Nimfrodian/Overlord/Documentation/RelayBoard/Waveshare_Modbus_RTU_Relay_8ch_board/wiki webpage/Modbus RTU Relay - Waveshare Wiki_files/Modbus-RTU-Relay-3.png

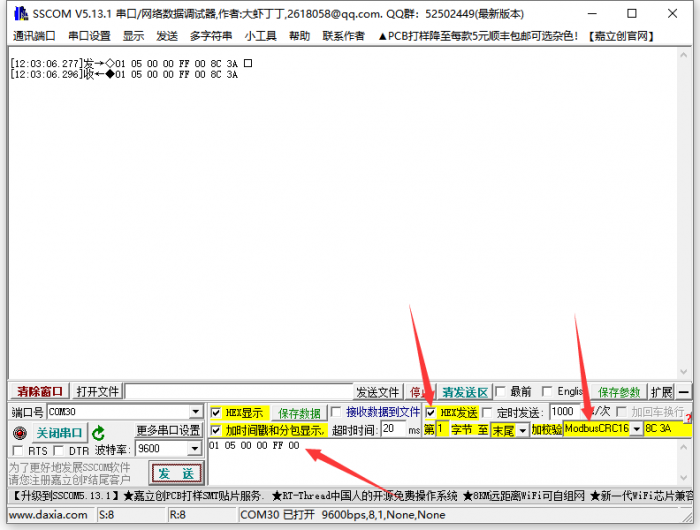
Documentation/RelayBoard/Waveshare_Modbus_RTU_Relay_8ch_board/wiki webpage/Modbus RTU Relay - Waveshare Wiki_files/Modbus-RTU-Relay-3.png
