Nimfrodian/Overlord/Documentation/RelayBoard/Waveshare_Modbus_RTU_Relay_8ch_board/wiki webpage/Modbus RTU Relay - Waveshare Wiki_files/Modbus-RTU-Relay_connet.jpg

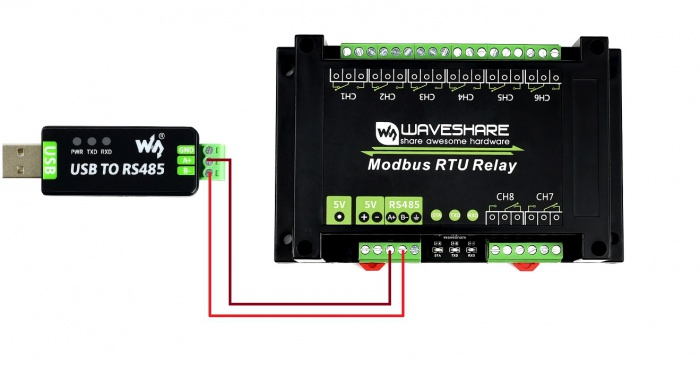
Documentation/RelayBoard/Waveshare_Modbus_RTU_Relay_8ch_board/wiki webpage/Modbus RTU Relay - Waveshare Wiki_files/Modbus-RTU-Relay_connet.jpg
