Nimfrodian/Overlord/other/tsmasterWorkspace/MiniProgram/h/TSMaster.h

#ifndef _TSMaster_MP_H
#define _TSMaster_MP_H

/*
  Note: 
  [1] Definitions of TCAN, TCANFD, TLIN, TFlexRay, TEthernetHeader can be found in this header
  [2] channel index is always starting from 0
  [3] for error codes of API, please see bottem area of this file
  [4] F3 for fast locating: TCAN TCANFD TLIN TFlexRay TEthernetHeader _TTSApp _TTSCOM _TTSTest
*/

#include <stdio.h>
#include <cstring>

#define CH1 0
#define CH2 1
#define CH3 2
#define CH4 3
#define CH5 4
#define CH6 5
#define CH7 6
#define CH8 7
#define CH9 8
#define CH10 9
#define CH11 10
#define CH12 11
#define CH13 12
#define CH14 13
#define CH15 14
#define CH16 15
#define CH17 16
#define CH18 17
#define CH19 18
#define CH20 19
#define CH21 20
#define CH22 21
#define CH23 22
#define CH24 23
#define CH25 24
#define CH26 25
#define CH27 26
#define CH28 27
#define CH29 28
#define CH30 29
#define CH31 30
#define CH32 31

#define GENERIC_STRING_MAX_LENGTH 32

typedef enum {lvlError = 1, lvlWarning = 2, lvlOK = 3, lvlHint = 4, lvlInfo = 5, lvlVerbose = 6} TLogLevel;

// basic var type definition
typedef unsigned __int8 u8;
typedef signed __int8 s8;
typedef unsigned __int16 u16;
typedef signed __int16 s16;
typedef unsigned __int32 u32;
typedef signed __int32 s32;
typedef unsigned __int64 u64;
typedef signed __int64 s64;
// pointer definition
typedef unsigned __int8* pu8;
typedef unsigned __int8** ppu8;
typedef signed __int8* ps8;
typedef unsigned __int16* pu16;
typedef signed __int16* ps16;
typedef unsigned __int32* pu32;
typedef signed __int32* ps32;
typedef signed __int32** pps32;
typedef unsigned __int64* pu64;
typedef signed __int64* ps64;
typedef float* pfloat;
typedef double* pdouble;
typedef char* pchar;
typedef char** ppchar;
typedef bool* pbool;
typedef void* pvoid;
#ifdef _WIN64
    typedef s64 native_int;
    typedef u64 ts_nfds_t;
#else
    typedef s32 native_int;
    typedef u32 ts_nfds_t;
#endif
typedef native_int* pnative_int;
typedef u32 ts_socket_t;
typedef unsigned __int32 tts_socklen_t;
typedef unsigned __int32* pts_socklen_t;
typedef u8 ts_sa_family_t;
typedef u16 ts_in_port_t;
typedef u32 ts_in_addr_t;


#define MIN(a,b) (((a)<(b))?(a):(b))
#define MAX(a,b) (((a)>(b))?(a):(b))
#define SWAP_BYTES(x) (((x) >> 8) | ((x & 0xFF) << 8))
#if defined(_MSC_VER)
    #define DLLEXPORT extern "C" __declspec(dllexport)
#else
    #define DLLEXPORT extern "C" __attribute__((visibility("default")))
#endif

#pragma pack(push)
#pragma pack(1)

// CAN definitions
#define MASK_CANProp_DIR_TX 0x01
#define MASK_CANProp_REMOTE 0x02
#define MASK_CANProp_EXTEND 0x04
#define MASK_CANProp_ERROR  0x80
#define MASK_CANProp_LOGGED 0x60

// CAN FD message properties
#define MASK_CANFDProp_IS_FD 0x01
#define MASK_CANFDProp_IS_EDL MASK_CANFDProp_IS_FD
#define MASK_CANFDProp_IS_BRS 0x02
#define MASK_CANFDProp_IS_ESI 0x04

// LIN message properties
#define MASK_LINProp_DIR_TX         0x01
#define MASK_LINProp_SEND_BREAK     0x02
#define MASK_LINProp_RECEIVED_BREAK 0x04
#define MASK_LINProp_SEND_SYNC      0x80
#define MASK_LINProp_RECEIVED_SYNC  0x10

const u8 DLC_DATA_BYTE_CNT[16] = {
    0, 1, 2, 3, 4, 5, 6, 7,
    8, 12, 16, 20, 24, 32, 48, 64
};

typedef enum _MBDDataType {
  dtInherit = 0, 
  dtDouble,
  dtSingle,
  dtHalf,
  dtInt8,
  dtUInt8,
  dtInt16,
  dtUInt16,
  dtInt32,
  dtUInt32,
  dtInt64,
  dtUInt64,
  dtBoolean,
  dtString,
} TMBDDataType, *PMBDDataType;

typedef struct _tip4_addr_t{
  u32 addr;
}tip4_addr_t, *pip4_addr_t;

typedef struct _tip6_addr_t{
  u32 addr[4];
  u32 zone;
}tip6_addr_t, *pip6_addr_t;

typedef enum {IPADDR_TYPE_V4 = 0, IPADDR_TYPE_V6 = 6, IPADDR_TYPE_ANY = 46} lwip_ip_addr_type;

typedef struct _tip_addr_t{
   tip6_addr_t ip4Or6;
   u32 FType;
   pip4_addr_t ipv4(void){
      return (pip4_addr_t)(&ip4Or6.addr[0]);
   }
   pip6_addr_t ipv6(void){
      return (pip6_addr_t)(&ip4Or6);
   }
}tip_addr_t, *pip_addr_t;

typedef struct _tts_sockaddr_private{
  u8 sa_len;
  ts_sa_family_t sa_family;
  char sa_data[14];
}tts_sockaddr_private, *pts_sockaddr;

typedef struct _ts_in_addr{
  ts_in_addr_t ts_addr;
}ts_in_addr;

#define   SIN_ZERO_LEN        (8)
typedef struct _tts_sockaddr_in_private{
  u8 sin_len;
  ts_sa_family_t sin_family;
  ts_in_port_t sin_port;
  ts_in_addr sin_addr;
  char sin_zero[SIN_ZERO_LEN];
}tts_sockaddr_in_private, pts_sockaddr_in;


typedef struct _ts_sockaddr_in_union{
  u32 FData[4];
}ts_sockaddr_in_union;

typedef struct _tts_iovec{
  void* iov_base;
  native_int iov_len;
}tts_iovec, *pts_iovec;

typedef struct _tts_timeval{
  s32 tv_sec;
  s32 tv_usec;
}tts_timeval, *pts_timeval;

#define TS_FD_SETSIZE 10
typedef struct _tts_fd_set{
  u8 fd_bits[2];
}tts_fd_set, *pts_fd_set;

typedef struct _tts_pollfd{
  s32 fd;
  s16 events; //short;
  s16 revents; //Short;
}tts_pollfd, *pts_pollfd;

typedef struct _tts_msghdr{ 
  pvoid msg_name;
  tts_socklen_t msg_namelen;
  s32 reserved0;
  pts_iovec msg_iov;
  s32 msg_iovlen;    //received package num
  s32 reserved1;
  pvoid msg_control;
  tts_socklen_t msg_controllen;
  s32 msg_flags;     //set internal
}tts_msghdr, *pts_msghdr;

typedef struct _tts_cmsghdr{
    tts_socklen_t cmsg_len;   ///* number of bytes, including header */
    s32 cmsg_level; ///* originating protocol */
    s32 cmsg_type;  ///* protocol-specific type */
}tts_cmsghdr, *pts_cmsghdr;

typedef struct _tts_in_pktinfo{
  u32 ipi_ifindex;     // Interface index
  ts_in_addr ipi_addr; // Destination (from header) address
}tts_in_pktinfo, *pts_in_pktinfo;

typedef struct _tts_addrinfo{
  s32 ai_flags;                         // Input flags
  s32 ai_family;                        // Address family of socket
  s32 ai_socktype;                      //Socket type
  s32 ai_protocol;                      // Protocol of socket
  tts_socklen_t  ai_addrlen;            // Length of socket address
  pts_sockaddr  ai_addr;                // Socket address of socket
  char*  ai_canonname;              // Canonical name of service location
  struct _tts_addrinfo*  ai_next;       // Pointer to next in list
}tts_addrinfo, *pts_addrinfo, **ppts_addrinfo;

typedef struct _tts_hostent{
  char*  h_name;          // Official name of the host
  char** h_aliases;       // A pointer to an array of pointers to alternative host names// terminated by a null pointer
  s32    h_addrtype;      // Address type
  s32    h_length;        // The length, in bytes, of the address
  char** h_addr_list;     // A pointer to an array of pointers to network addresses (in
                          // network byte order) for the host, terminated by a null pointer
}tts_hostent, *pts_hostent, **ppts_hostent;

#define LWIP_IPV6_NUM_ADDRESSES 3
//packed =  1
typedef struct _tts_net_device{
  tip4_addr_t ip_addr;
  tip4_addr_t netmask;
  tip4_addr_t gw;
  tip6_addr_t ip6_addr[LWIP_IPV6_NUM_ADDRESSES];
  u16 mtu;
  u16 mtu6;
  u16 vlan;
  u8 hwaddr[6];
  u8 flags;
  u8 index;
}tts_net_device, *pts_net_device, **ppts_net_device;

     
// CAN frame type ================================================
typedef struct _TCAN{
    u8 FIdxChn;
    u8 FProperties;
    u8 FDLC;
    u8 FReserved;
    s32 FIdentifier;
    s64 FTimeUs;
    u8  FData[8];
    // is_tx -----------------------------------------------------
    bool get_is_tx(void)
    { 
        return (FProperties & MASK_CANProp_DIR_TX) != 0;
    }
    void set_is_tx(const bool value)
    {
        if (value) {
            FProperties = FProperties | MASK_CANProp_DIR_TX;
        } else {
            FProperties = FProperties & (~MASK_CANProp_DIR_TX);
        }
    }
    __declspec(property(get = get_is_tx, put = set_is_tx)) bool is_tx;
    // is_data ----------------------------------------------------
    bool get_is_data(void)
    { 
        return (FProperties & MASK_CANProp_REMOTE) == 0;
    }
    void set_is_data(const bool value)
    {
        if (value) {
            FProperties = FProperties & (~MASK_CANProp_REMOTE);
        } else {
            FProperties = FProperties | MASK_CANProp_REMOTE;
        }
    }
    __declspec(property(get = get_is_data, put = set_is_data)) bool is_data;
    // is_std -----------------------------------------------------
    bool get_is_std(void)
    { 
        return (FProperties & MASK_CANProp_EXTEND) == 0;
    }
    void set_is_std(const bool value)
    {
        if (value) {
            FProperties = FProperties & (~MASK_CANProp_EXTEND);
        } else {
            FProperties = FProperties | MASK_CANProp_EXTEND;
        }
    }
    __declspec(property(get = get_is_std, put = set_is_std)) bool is_std;
    // is_err ----------------------------------------------------
    bool get_is_err(void)
    { 
        return (FProperties & MASK_CANProp_ERROR) != 0;
    }
    void set_is_err(const bool value)
    {
        if (value) {
            FProperties = FProperties | MASK_CANProp_ERROR;
        } else {
            FProperties = FProperties & (~MASK_CANProp_ERROR);
        }
    }
    __declspec(property(get = get_is_err, put = set_is_err)) bool is_err;
    // load data bytes -------------------------------------------
    void load_data(u8* a) {
        for (u32 i = 0; i < 8; i++) {
            FData[i] = *a++;
        }
    }
    void set_data(const u8 d0, const u8 d1, const u8 d2, const u8 d3, const u8 d4, const u8 d5, const u8 d6, const u8 d7){
        FData[0] = d0;
        FData[1] = d1;
        FData[2] = d2;
        FData[3] = d3;
        FData[4] = d4;
        FData[5] = d5;
        FData[6] = d6;
        FData[7] = d7;
    }
    // initialize with standard identifier -----------------------
    void init_w_std_id(s32 AId, s32 ADLC) {
        FIdxChn = 0;
        FIdentifier = AId;
        FDLC = ADLC;
        FReserved = 0;
        FProperties = 0;
        is_tx = false;
        is_std = true;
        is_data = true;
        *(u64*)(&FData[0]) = 0;
        FTimeUs = 0;
    }
    // initialize with extended identifier -----------------------
    void init_w_ext_id(s32 AId, s32 ADLC) {
        FIdxChn = 0;
        FIdentifier = AId;
        FDLC = ADLC;
        FReserved = 0;
        FProperties = 0;
        is_tx = false;
        is_std = false;
        is_data = true;
        *(u64*)(&FData[0]) = 0;
        FTimeUs = 0;
    }
} TCAN, *PCAN;

// CAN FD frame type =============================================
typedef struct _TCANFD{
    u8 FIdxChn;
    u8 FProperties;
    u8 FDLC;
    u8 FFDProperties;
    s32 FIdentifier;
    s64 FTimeUs;
    u8  FData[64];
    // is_tx -----------------------------------------------------
    bool get_is_tx(void)
    { 
        return (FProperties & MASK_CANProp_DIR_TX) != 0;
    }
    void set_is_tx(const bool value)
    {
        if (value) {
            FProperties = FProperties | MASK_CANProp_DIR_TX;
        } else {
            FProperties = FProperties & (~MASK_CANProp_DIR_TX);
        }
    }
    __declspec(property(get = get_is_tx, put = set_is_tx)) bool is_tx;
    // is_data ---------------------------------------------------
    bool get_is_data(void)
    { 
        return (FProperties & MASK_CANProp_REMOTE) == 0;
    }
    void set_is_data(const bool value)
    {
        if (value) {
            FProperties = FProperties & (~MASK_CANProp_REMOTE);
        } else {
            FProperties = FProperties | MASK_CANProp_REMOTE;
        }
    }
    __declspec(property(get = get_is_data, put = set_is_data)) bool is_data;
    // is_std ----------------------------------------------------
    bool get_is_std(void)
    { 
        return (FProperties & MASK_CANProp_EXTEND) == 0;
    }
    void set_is_std(const bool value)
    {
        if (value) {
            FProperties = FProperties & (~MASK_CANProp_EXTEND);
        } else {
            FProperties = FProperties | MASK_CANProp_EXTEND;
        }
    }
    __declspec(property(get = get_is_std, put = set_is_std)) bool is_std;
    // is_err ----------------------------------------------------
    bool get_is_err(void)
    { 
        return (FProperties & MASK_CANProp_ERROR) != 0;
    }
    void set_is_err(const bool value)
    {
        if (value) {
            FProperties = FProperties | MASK_CANProp_ERROR;
        } else {
            FProperties = FProperties & (~MASK_CANProp_ERROR);
        }
    }
    __declspec(property(get = get_is_err, put = set_is_err)) bool is_err;
    // is_edl ----------------------------------------------------
    bool get_is_edl(void)
    { 
        return (FFDProperties & MASK_CANFDProp_IS_FD) != 0;
    }
    void set_is_edl(const bool value)
    {
        if (value) {
            FFDProperties = FFDProperties | MASK_CANFDProp_IS_FD;
        } else {
            FFDProperties = FFDProperties & (~MASK_CANFDProp_IS_FD);
        }
    }
    __declspec(property(get = get_is_edl, put = set_is_edl)) bool is_edl;
    // is_brs ----------------------------------------------------
    bool get_is_brs(void)
    { 
        return (FFDProperties & MASK_CANFDProp_IS_BRS) != 0;
    }
    void set_is_brs(const bool value)
    {
        if (value) {
            FFDProperties = FFDProperties | MASK_CANFDProp_IS_BRS;
        } else {
            FFDProperties = FFDProperties & (~MASK_CANFDProp_IS_BRS);
        }
    }
    __declspec(property(get = get_is_brs, put = set_is_brs)) bool is_brs;
    // is_esi ----------------------------------------------------
    bool get_is_esi(void)
    { 
        return (FFDProperties & MASK_CANFDProp_IS_ESI) != 0;
    }
    void set_is_esi(const bool value)
    {
        if (value) {
            FFDProperties = FFDProperties | MASK_CANFDProp_IS_ESI;
        } else {
            FFDProperties = FFDProperties & (~MASK_CANFDProp_IS_ESI);
        }
    }
    __declspec(property(get = get_is_esi, put = set_is_esi)) bool is_esi;
    // load data bytes -------------------------------------------
    void load_data(u8* a) {
        for (u32 i = 0; i < 64; i++) {
            FData[i] = *a++;
        }
    }
    // initialize with standard identifier -----------------------
    void init_w_std_id(s32 AId, s32 ADLC) {
        s32 i;
        FIdxChn = 0;
        FIdentifier = AId;
        FDLC = ADLC;
        FProperties = 0;
        FFDProperties = MASK_CANFDProp_IS_FD;
        is_tx = false;
        is_std = true;
        is_data = true;
        for (i = 0; i < 64; i++) FData[i] = 0;
        FTimeUs = 0;
    }
    // initialize with extended identifier -----------------------
    void init_w_ext_id(s32 AId, s32 ADLC) {
        s32 i;
        FIdxChn = 0;
        FIdentifier = AId;
        FDLC = ADLC;
        FFDProperties = MASK_CANFDProp_IS_FD;
        FProperties = 0;
        is_tx = false;
        is_std = false;
        is_data = true;
        for (i = 0; i < 64; i++) FData[i] = 0;
        FTimeUs = 0;
    }
    // get fd data length ----------------------------------------
    s32 get_data_length() {
        s32 l = MIN(FDLC, 15);
        l = MAX(l, 0);
        return DLC_DATA_BYTE_CNT[l];
    }
    // to CAN struct ---------------------------------------------
    TCAN to_tcan(void){
        return *(TCAN*)(&FIdxChn);
    }
} TCANFD, *PCANFD;

// LIN frame type ================================================
typedef struct _LIN {
    u8  FIdxChn;
    u8  FErrStatus;
    u8  FProperties;
    u8  FDLC;
    u8  FIdentifier;
    u8  FChecksum;
    u8  FStatus;
    s64 FTimeUs;
    u8  FData[8];
    // is_tx -----------------------------------------------------
    bool get_is_tx(void)
    {
        return (FProperties & MASK_LINProp_DIR_TX) != 0;
    }
    void set_is_tx(const bool value)
    {
        if (value) {
            FProperties = FProperties | MASK_LINProp_DIR_TX;
        }
        else {
            FProperties = FProperties & (~MASK_LINProp_DIR_TX);
        }
    }
    __declspec(property(get = get_is_tx, put = set_is_tx)) bool is_tx;
    // load data bytes -------------------------------------------
    void load_data(u8* a) {
        for (u32 i = 0; i < 8; i++) {
            FData[i] = *a++;
        }
    }
    // initialize with identifier --------------------------------
    void init_w_id(const s32 AId, const s32 ADLC) {
        FIdxChn = 0;
        FErrStatus = 0;
        FProperties = 0;
        FDLC = ADLC;
        FIdentifier = AId;
        *(__int64*)(&FData[0]) = 0;
        FChecksum = 0;
        FStatus = 0;
        FTimeUs = 0;
    }
}TLIN, *PLIN;

// FlexRay Frame Type ============================================
typedef struct _TFlexRay {
    u8  FIdxChn;               // channel index starting from 0
    u8  FChannelMask;          // 0: reserved, 1: A, 2: B, 3: AB
    u8  FDir;                  // 0: Rx, 1: Tx, 2: Tx Request
    u8  FPayloadLength;        // payload length in bytes
    u8  FActualPayloadLength;  // actual data bytes
    u8  FCycleNumber;          // cycle number: 0~63
    u8  FCCType;               // 0 = Architecture independent, 1 = Invalid CC type, 2 = Cyclone I, 3 = BUSDOCTOR, 4 = Cyclone II, 5 = Vector VN interface, 6 = VN - Sync - Pulse(only in Status Event, for debugging purposes only)
    u8  FFrameType;            // 0 = raw flexray frame, 1 = error event, 2 = status, 3 = start cycle
    u16 FHeaderCRCA;           // header crc A
    u16 FHeaderCRCB;           // header crc B
    u16 FFrameStateInfo;       // bit 0~15, error flags
    u16 FSlotId;               // static seg: 0~1023
    u32 FFrameFlags;           // bit 0~22
                               // 0 1 = Null frame.
                               // 1 1 = Data segment contains valid data
                               // 2 1 = Sync bit
                               // 3 1 = Startup flag
                               // 4 1 = Payload preamble bit
                               // 5 1 = Reserved bit
                               // 6 1 = Error flag(error frame or invalid frame)
                               // 7 Reserved
                               // 15 1 = Async.monitoring has generated this event
                               // 16 1 = Event is a PDU
                               // 17 Valid for PDUs only.The bit is set if the PDU is valid(either if the PDU has no update bit, or the update bit for the PDU was set in the received frame).
                               // 18 Reserved
                               // 19 1 = Raw frame(only valid if PDUs are used in the configuration).A raw frame may contain PDUs in its payload
                               // 20 1 = Dynamic segment    0 = Static segment
                               // 21 This flag is only valid for frames and not for PDUs.    1 = The PDUs in the payload of this frame are logged in separate logging entries. 0 = The PDUs in the payload of this frame must be extracted out of this frame.The logging file does not contain separate  // PDU - entries.
                               // 22 Valid for PDUs only.The bit is set if the PDU has an update bit
    u32 FFrameCRC;             // frame crc
    u64 FReserved1;            // 8 reserved bytes
    u64 FReserved2;            // 8 reserved bytes
    u64 FTimeUs;               // timestamp in us
    u8  FData[254];            // 254 data bytes
    // is_tx -----------------------------------------------------
    bool get_is_tx(void){
        return FDir != 0;
    }
    void set_is_tx(const bool value){
        if (value) {
            FDir = 1;
        } else {
            FDir = 0;
        }
    }
    __declspec(property(get = get_is_tx, put = set_is_tx)) bool is_tx;
    // is_null ---------------------------------------------------
    bool get_is_null(void){
        return (FFrameFlags & ((u32)1 << 0)) != 0;
    }
    void set_is_null(const bool value){
        if (value) {
            FFrameFlags |= ((u32)1 << 0);
        } else {
            FFrameFlags &= ~((u32)1 << 0);
        }
    }
    __declspec(property(get = get_is_null, put = set_is_null)) bool is_null;
    // is_data ---------------------------------------------------
    bool get_is_data(void){
        return (FFrameFlags & ((u32)1 << 1)) != 0;
    }
    void set_is_data(const bool value){
        if (value) {
            FFrameFlags |= ((u32)1 << 1);
        } else {
            FFrameFlags &= ~((u32)1 << 1);
        }
    }
    __declspec(property(get = get_is_data, put = set_is_data)) bool is_data;
    // is_sync ---------------------------------------------------
    bool get_is_sync(void){
        return (FFrameFlags & ((u32)1 << 2)) != 0;
    }
    void set_is_sync(const bool value){
        if (value) {
            FFrameFlags |= ((u32)1 << 2);
        } else {
            FFrameFlags &= ~((u32)1 << 2);
        }
    }
    __declspec(property(get = get_is_sync, put = set_is_sync)) bool is_sync;
    // is_startup ------------------------------------------------
    bool get_is_startup(void){
        return (FFrameFlags & ((u32)1 << 3)) != 0;
    }
    void set_is_startup(const bool value){
        if (value) {
            FFrameFlags |= ((u32)1 << 3);
        } else {
            FFrameFlags &= ~((u32)1 << 3);
        }
    }
    __declspec(property(get = get_is_startup, put = set_is_startup)) bool is_startup;
    // is_pp -----------------------------------------------------
    bool get_is_pp(void){
        return (FFrameFlags & ((u32)1 << 4)) != 0;
    }
    void set_is_pp(const bool value){
        if (value) {
            FFrameFlags |= ((u32)1 << 4);
        } else {
            FFrameFlags &= ~((u32)1 << 4);
        }
    }
    __declspec(property(get = get_is_pp, put = set_is_pp)) bool is_pp;
    // is_err ----------------------------------------------------
    bool get_is_err(void){
        return (FFrameFlags & ((u32)1 << 6)) != 0;
    }
    void set_is_err(const bool value){
        if (value) {
            FFrameFlags |= ((u32)1 << 6);
        } else {
            FFrameFlags &= ~((u32)1 << 6);
        }
    }
    __declspec(property(get = get_is_err, put = set_is_err)) bool is_err;
    // is_static_segment -----------------------------------------
    bool get_is_static_segment(void){
        return (FFrameFlags & ((u32)1 << 20)) != 0;
    }
    void set_is_static_segment(const bool value){
        if (value) {
            FFrameFlags |= ((u32)1 << 20);
        } else {
            FFrameFlags &= ~((u32)1 << 20);
        }
    }
    __declspec(property(get = get_is_static_segment, put = set_is_static_segment)) bool is_static_segment;
    // initialize with slot id -----------------------------------
    void init_w_slot_id(const s32 ASlotId, const s32 ADLC) {
        FIdxChn = 0;
        FChannelMask = 1;
        FDir = 0;
        FPayloadLength = ADLC;
        FActualPayloadLength = ADLC;
        FCycleNumber = 0;
        FCCType = 5;
        FFrameType = 0;
        FHeaderCRCA = 0;
        FHeaderCRCB = 0;
        FFrameStateInfo = 0;
        FFrameFlags = 1 << 1; // data frame
        FSlotId = ASlotId;
        FFrameCRC = 0;
        FReserved1 = 0;
        FReserved2 = 0;
        FTimeUs = 0;
        for (u32 i = 0; i < 254; i++) {
            FData[i] = 0;
        }
    }
    // load data bytes -------------------------------------------
    void load_data(u8* a) {
        for (u32 i = 0; i < 254; i++) {
            FData[i] = *a++;
        }
    }
} TFlexRay, *PFlexRay;

// Ethernet Frame Type
typedef struct _TEthernetHeader{ // size = 24 B
    u8  FIdxChn;                 // Application channel index starting from 0 = Network index
    u8  FIdxSwitch;              // Network's switch index
    u8  FIdxPort;                // Network's switch's port index, 0~127: measurement port, 128~255: virtual port
    u8  FConfig;                 // 0-1: 0 = Rx, 1 = Tx, 2 = TxRq
                                 // 2: crc status, for tx, 0: crc is included in data, 1: crc is not included in data
                                 //                for rx, 0: crc is ok, 1: crc is not ok
                                 // 3: tx done type, 0: only report timestamp, 1: report full info(header+frame)
    u16 FEthernetPayloadLength;  // Length of Ethernet payload data in bytes. Max 1582 (1600 packet length - 18 header) data bytes per frame
    u16 FReserved;               // reserved for padding
    u64 FTimeUs;                 // timestamp in us
    pu8 FEthernetDataAddr;       // Ethernet data (from destination MAC to ending of payload)
#ifndef _WIN64
    u32 FPadding;                // to be compatible with x64
#endif
    u8 get_Payloads(const int index) {
        return *(ethernet_payload_addr() + index);
    }
    void set_Payloads(const int index, const u8 value) {
        *(ethernet_payload_addr() + index) = value;
    }
    __declspec(property(get = get_Payloads, put = set_Payloads)) u8 Payloads[];
    inline bool get_tx() {
        return (FConfig & 0x1) != 0;
    }
    inline void set_tx(bool a) {
        if (a) {
            FConfig |= 1;
        } else {
            FConfig &= 0xFC;
        }
    }
    void reset_data_pointer(){
        FEthernetDataAddr = actual_data_pointer();
    }
    void init(const u16 APayloadLength){
        FIdxChn = 0;
        FIdxSwitch = 0;
        FIdxPort = 0;
        FConfig = 0;
        FEthernetPayloadLength = APayloadLength;
        FReserved = 0;
        FTimeUs = 0;
        reset_data_pointer();
#ifndef _WIN64
        FPadding = 0;
#endif
        s32 i;
        pu8 p = FEthernetDataAddr;
        s32 n = MIN(1612 - 14, APayloadLength);
        n += 14;
        for (i=0; i<n; i++){
            *p++ = 0;
        }
        *(pu16)(ethernet_type_addr()) = 0x00; // IPV4 = SWAP_BYTES(0x0800)
        p = destination_mac_addr();
        for (i=0; i<6; i++){
            *p++ = 0xFF;
        }
    }
    bool is_virtual(){
        return FIdxPort >= 128;
    }
    bool is_ip_frame(){
        return ethernet_type() == 0x0800;
    }
    bool is_tcp_frame(){
        u16 o;
        has_vlans(&o);
        return (ethernet_type() == 0x0800) && (0x06 == *(FEthernetDataAddr + 0x17 + o));
    }
    bool is_udp_frame(){
        u16 o;
        has_vlans(&o);
        return (ethernet_type() == 0x0800) && (0x11 == *(FEthernetDataAddr + 0x17 + o));
    }
    pu16 first_vlan_addr(){
        return (pu16)(actual_data_pointer() + 6 + 6);
    }
    bool has_vlans(pu16 AOffsetBytes){
        *AOffsetBytes = 0;
        while (*(pu16)(actual_data_pointer() + 6 + 6 + (*AOffsetBytes)) == 0x0081){
            *AOffsetBytes = *AOffsetBytes + 4;
        }
        return *AOffsetBytes > 0;
    }
    pu8 actual_data_pointer() {
        return &FIdxChn + sizeof(_TEthernetHeader);
    }
    s32 total_ethernet_packet_length() {
        u16 o;
        has_vlans(&o);
        return sizeof(_TEthernetHeader) + 6 + 6 + 2 + o + FEthernetPayloadLength;
    }
    s32 ethernet_data_length(){
        u16 o;
        has_vlans(&o);
        return FEthernetPayloadLength + 6 + 6 + o + 2;
    }
    void set_ethernet_data_length(const u16 ALength) {
        u16 o;
        has_vlans(&o);
        o += 14;
        if (ALength > o){
            FEthernetPayloadLength = ALength - o;
        }
    }
    pu8 ethernet_payload_addr() {
        u16 o;
        has_vlans(&o);
        return FEthernetDataAddr + 6 + 6 + 2 + o;
    }
    pu8 destination_mac_addr() {
        return FEthernetDataAddr;
    }
    pu8 source_mac_addr() {
        return FEthernetDataAddr + 6;
    }
    pu8 destination_ip_addr(){
        if (!is_ip_frame()) return nullptr;
        u16 o;
        has_vlans(&o);
        return FEthernetDataAddr + 0x1E + o;
    }
    pu8 source_ip_addr(){
        if (!is_ip_frame()) return nullptr;
        u16 o;
        has_vlans(&o);
        return FEthernetDataAddr + 0x1A + o;
    }
    u16 destination_port_value(){
        if (!is_ip_frame()) return 0;
        u16 o;
        has_vlans(&o);
        o = *(u16*)(FEthernetDataAddr + 0x24 + o);
        return SWAP_BYTES(o);
    }
    u16 source_port_value(){
        if (!is_ip_frame()) return 0;
        u16 o;
        has_vlans(&o);
        o = *(u16*)(FEthernetDataAddr + 0x22 + o);
        return SWAP_BYTES(o);
    }
    pu16 ethernet_type_addr() {
        u16 o;
        has_vlans(&o);
        pu8 p = FEthernetDataAddr + 6 + 6 + o;
        return (pu16)(p);
    }
    u16 ethernet_type() {
        u16 t = *(pu16)(ethernet_type_addr());
        return SWAP_BYTES(t);
    }
    u16 get_ip_header_checksum(){
        u16 o;
        if (!is_ip_frame()) return 0;
        has_vlans(&o);
        o = *(pu16)(FEthernetDataAddr + 0x18 + o);
        return SWAP_BYTES(o);
    }
    void set_ip_header_checksum(const u16 AValue){
        u16 o;
        if (!is_ip_frame()) return;
        has_vlans(&o);
        *(pu16)(FEthernetDataAddr + 0x18 + o) = SWAP_BYTES(AValue);
    }
    void copy_payload(const pu8 ABuffer, const u16 ALength){
        u16 l = MIN(ALength, FEthernetPayloadLength);
        std::memcpy(ethernet_payload_addr(), ABuffer, l);
    }
    void set_ip_packet_payload_length(const u16 ALength){
        u16 o;
        if (!is_ip_frame()) return;
        has_vlans(&o);
        *(pu16)(FEthernetDataAddr + 16 + o) = SWAP_BYTES(ALength + 20);
    }
    u16 get_ip_packet_payload_length(){
        u16 o;
        if (!is_ip_frame()) return 0;
        has_vlans(&o);
        o = *(pu16)(FEthernetDataAddr + 16 + o);
        return SWAP_BYTES(o) - 20;
    }
    pu8 get_ip_packet_data_addr(){
        u16 o;
        if (!is_ip_frame()) return nullptr;
        has_vlans(&o);
        return FEthernetDataAddr + 0x0E + o;
    }
    pu8 get_ip_packet_payload_addr(){
        u16 o;
        if (!is_ip_frame()) return nullptr;
        has_vlans(&o);
        return FEthernetDataAddr + 0x22 + o;
    }
    void set_udp_payload_length(const u16 ALength){
        u16 o;
        if (!is_udp_frame()) return;
        has_vlans(&o);
        *(pu16)(FEthernetDataAddr + 0x26 + o) = SWAP_BYTES(ALength + 8/*header length*/);
    }
    u16 get_udp_payload_length(){
        u16 o;
        if (!is_udp_frame()) return 0;
        has_vlans(&o);
        o = *(pu16)(FEthernetDataAddr + 0x26 + o);
        return SWAP_BYTES(o) - 8/*header length*/;
    }
    pu8 get_ip_address_destination_addr(){
        u16 o;
        if (!is_ip_frame()) return 0;
        has_vlans(&o);
        return FEthernetDataAddr + 0x1E + o;
    }
    pu8 get_ip_address_source_addr(){
        u16 o;
        if (!is_ip_frame()) return 0;
        has_vlans(&o);
        return FEthernetDataAddr + 0x1A + o;
    }
    u16 get_udp_port_destination(){
        u16 o;
        if (!is_udp_frame()) return 0;
        has_vlans(&o);
        o = *(pu16)(FEthernetDataAddr + 0x24 + o);
        return SWAP_BYTES(o);
    }
    u16 get_udp_port_source(){
        u16 o;
        if (!is_udp_frame()) return 0;
        has_vlans(&o);
        o = *(pu16)(FEthernetDataAddr + 0x22 + o);
        return SWAP_BYTES(o);
    }
    void set_udp_port_destination(const u16 AValue){
        u16 o;
        if (!is_udp_frame()) return;
        has_vlans(&o);
        *(pu16)(FEthernetDataAddr + 0x24 + o) = SWAP_BYTES(AValue);
    }
    void set_udp_port_source(const u16 AValue){
        u16 o;
        if (!is_udp_frame()) return;
        has_vlans(&o);
        *(pu16)(FEthernetDataAddr + 0x22 + o) = SWAP_BYTES(AValue);
    }
    bool check_udp_fragment(pu16 AId, pu16 AOffset){
        u16 o;
        bool r;
        has_vlans(&o);
        r = (0x40 & *(FEthernetDataAddr + 0x14 + o)) == 0;
        if (r) {
            *AOffset = *(pu16)(FEthernetDataAddr + 0x14 + o);
            *AOffset = (SWAP_BYTES(*AOffset) & 0x1FFF) << 3;
            *AId = *(pu16)(FEthernetDataAddr + 0x12 + o);
            *AId = SWAP_BYTES(*AId);
        }
        return r;
    }
    pu8 get_udp_payload_addr(){
        u16 o, id, fo;
        if (!is_udp_frame()) return nullptr;        
        if (check_udp_fragment(&id, &fo)){
            if (fo > 0){
                return get_ip_packet_data_addr();
            }
        }
        has_vlans(&o);
        return FEthernetDataAddr + 0x2A + o;
    }
} TEthernetHeader, *PEthernetHeader;
typedef struct _TEthernetMAX {
    TEthernetHeader FHeader;
    u8 FBytes[1612];
    void reset_data_pointer(){
        FHeader.FEthernetDataAddr = FHeader.actual_data_pointer();
    }
} TEthernetMAX, *PEthernetMAX;

// FlexRay Cluster Parameters (size = 440)
typedef struct _TFlexRayClusterParameters {
    // general parameters
    char FShortName[GENERIC_STRING_MAX_LENGTH];
    char FLongName[GENERIC_STRING_MAX_LENGTH];
    char FDescription[GENERIC_STRING_MAX_LENGTH];
    char FSpeed[GENERIC_STRING_MAX_LENGTH];
    char FChannels[GENERIC_STRING_MAX_LENGTH];
    char FBitCountingPolicy[GENERIC_STRING_MAX_LENGTH];
    char FProtocol[GENERIC_STRING_MAX_LENGTH];
    char FProtocolVersion[GENERIC_STRING_MAX_LENGTH];
    char FMedium[GENERIC_STRING_MAX_LENGTH];
    int FIsHighLowBitOrder;
    int FMaxFrameLengthByte;
    int FNumberOfCycles;
    // cycle parameters
    int FCycle_us;
    double FBit_us;
    double FSampleClockPeriod_us;
    double FMacrotick_us;
    int FMacroPerCycle;
    int FNumberOfStaticSlots;
    int FStaticSlot_MT;
    int FActionPointOffset_MT;
    int FTSSTransmitter_gdBit;
    int FPayloadLengthStatic_WORD;
    int FNumberOfMiniSlots;
    int FMiniSlot_MT;
    int FMiniSlotActionPointOffset_MT;
    int FDynamicSlotIdlePhase_MiniSlots;
    int FSymbolWindow_MT;
    int FNIT_MT;
    int FSyncNodeMax;
    int FNetworkManagementVectorLength;
    // Wakeup and startup parameters
    int FListenNoise;
    int FColdStartAttempts;
    int FCASRxLowMax_gdBit;
    int FWakeupSymbolRxIdle_gdBit;
    int FWakeupSymbolRxLow_gdBit;
    int FWakeupSymbolRxWindow_gdBit;
    int FWakeupSymbolTxIdle_gdBit;
    int FWakeupSymbolTxLow_gdBit;
    double FMaxInitializationError_us;
    // clock correction parameters
    int FClusterDriftDamping_uT;
    int FOffsetCorrectionStart_MT;
    int FMaxWithoutClockCorrectionFatal;
    int FMaxWithoutClockCorrectionPassive;
} TFlexRayClusterParameters, *PFlexRayClusterParameters;

// FlexRay Controller Parameters (size = 212)
typedef struct _TFlexRayControllerParameters {
    // general parameters
    char FShortName[GENERIC_STRING_MAX_LENGTH];
    char FConnectedChannels[GENERIC_STRING_MAX_LENGTH];
    // cycle parameters
    int FMicroPerCycle_uT;
    int FMicroPerMacroNom_uT;
    double FMicroTick_us;
    int FSamplesPerMicrotick;
    // wakeup & startup parameters
    int FWakeupChannelA;
    int FWakeupChannelB;
    int FMaxDrift_uT;
    int FWakeupPattern;
    int FListenTimeout_uT;
    int FAcceptedStartupRange_uT;
    int FMacroInitialOffsetA_MT;
    int FMacroInitialOffsetB_MT;
    int FMicroInitialOffsetA_uT;
    int FMicroInitialOffsetB_uT;
    // clock correction parameters
    char FKeySlotUsage[GENERIC_STRING_MAX_LENGTH];
    int FKeySlotID;
    int FSingleSlotEnabled;
    int FClusterDriftDamping_uT;
    int FDocodingCorrection_uT;
    int FDelayCompensationA_uT;
    int FDelayCompensationB_uT;
    int FOffsetCorrectionOut_uT;
    int FExternRateCorrection_uT;
    int FRateCorrectionOut_uT;
    int FExternOffsetCorrection_uT;
    int FAllowHaltDueToClock;
    int FAllowPassivToActive;
    // latesttx
    int FLatestTx;
    int FMaxDynamicPayloadLength;
} TFlexRayControllerParameters, *PFlexRayControllerParameters;

// Generic definitions ===========================================
typedef void (__stdcall* TProcedure)(const void* AObj);
typedef void (__stdcall* TProcedureSetInt)(const void* AObj, const s64 AValue);
typedef s64 (__stdcall* TIntFunction)(const void* AObj);
typedef void (__stdcall* TProcedureSetDouble)(const void* AObj, const double AValue);
typedef double (__stdcall* TDoubleFunction)(const void* AObj);
typedef void (__stdcall* TProcedureSetString)(const void* AObj, const char* AValue);
typedef char* (__stdcall* TStringFunction)(const void* AObj);
typedef void (__stdcall* TProcedureSetCAN)(const void* AObj, const PCAN AValue);
typedef TCAN (__stdcall* TTCANFunction)(const void* AObj);
typedef void (__stdcall* TProcedureSetCANFD)(const void* AObj, const PCANFD AValue);
typedef TCANFD (__stdcall* TTCANFDFunction)(const void* AObj);
typedef void (__stdcall* TProcedureSetLIN)(const void* AObj, const PLIN AValue);
typedef TLIN (__stdcall* TTLINFunction)(const void* AObj);
typedef void(__stdcall* TWriteAPIDocumentFunc)(const void* AOpaque, const char* AName, const char* AGroup, const char* ADesc, const char* AExample, const s32 AParaCount);
typedef void(__stdcall* TWriteAPIParaFunc)(const void* AOpaque, const s32 AIdx, const char* AAPIName, const char* AParaName, const bool AIsConst, const char* AParaType, const char* ADesc);                            

// TSMaster variable =============================================
typedef struct _TMPVarInt {
    void* FObj;
    TIntFunction internal_get;
    TProcedureSetInt internal_set;
    s64 get(void) {
        return internal_get(FObj);
    }
    void set(const s64 AValue) {
        internal_set(FObj, AValue);
    }
}TMPVarInt;

typedef struct _TMPVarDouble {
    void* FObj;
    TDoubleFunction internal_get;
    TProcedureSetDouble internal_set;
    double get(void) {
        return internal_get(FObj);
    }
    void set(const double AValue) {
        internal_set(FObj, AValue);
    }
}TMPVarDouble;

typedef struct _TMPVarString {
    void* FObj;
    TStringFunction internal_get;
    TProcedureSetString internal_set;
    char* get(void) {
        return internal_get(FObj);
    }
    void set(const char* AValue) {
        internal_set(FObj, AValue);
    }
}TMPVarString;

typedef struct _TMPVarCAN {
    void* FObj;
    TTCANFunction internal_get;
    TProcedureSetCAN internal_set;
    TCAN get(void) {
        return internal_get(FObj);
    }
    void set(TCAN AValue) {
        internal_set(FObj, &AValue);
    }
}TMPVarCAN;

typedef struct _TMPVarCANFD {
    void* FObj;
    TTCANFDFunction internal_get;
    TProcedureSetCANFD internal_set;
    TCANFD get(void) {
        return internal_get(FObj);
    }
    void set(TCANFD AValue) {
        internal_set(FObj, &AValue);
    }
}TMPVarCANFD;

typedef struct _TMPVarLIN {
    void* FObj;
    TTLINFunction internal_get;
    TProcedureSetLIN internal_set;
    TLIN get(void) {
        return internal_get(FObj);
    }
    void set(TLIN AValue) {
        internal_set(FObj, &AValue);
    }
}TMPVarLIN;

// TSMaster timer ================================================
// legacy timer before 2025-07-26
typedef struct _TMPTimerMS {
    void* FObj;
    TProcedure internal_start;
    TProcedure internal_stop;
    TProcedureSetInt internal_set_interval;
    TIntFunction internal_get_interval;
    void start(void) {
        internal_start(FObj);
    }
    void stop(void) {
        internal_stop(FObj);
    }
    void set_interval(const s64 AInterval) {
        internal_set_interval(FObj, AInterval);
    }
    s64 get_interval(void) {
        return internal_get_interval(FObj);
    }
}TMPTimerMS;

// timer with singleshot since 2025-07-26
typedef struct _TMPTimerMSUpg1 {
    void* FObj;
    TProcedure internal_start;
    TProcedure internal_stop;
    TProcedureSetInt internal_set_interval;
    TIntFunction internal_get_interval;
    TProcedure internal_start_singleshot;
    native_int FDummy[3]; 
    void start(void) {
        internal_start(FObj);
    }
    void stop(void) {
        internal_stop(FObj);
    }
    void set_interval(const s64 AInterval) {
        internal_set_interval(FObj, AInterval);
    }
    s64 get_interval(void) {
        return internal_get_interval(FObj);
    }
    void start_singleshot(void) {
        internal_start_singleshot(FObj);
    }
}TMPTimerMSUpg1;

// TSMaster application definition ===============================
#define APP_DEVICE_NAME_LENGTH 32
typedef enum _TLIBBusToolDeviceType{
    BUS_UNKNOWN_TYPE           = 0, 
    TS_TCP_DEVICE              = 1, 
    XL_USB_DEVICE              = 2, 
    TS_USB_DEVICE              = 3, 
    PEAK_USB_DEVICE            = 4,
    KVASER_USB_DEVICE          = 5,
    ZLG_USB_DEVICE             = 6,
    ICS_USB_DEVICE             = 7,
    TS_TC1005_DEVICE           = 8,
    CANABLE_USB_DEVICE         = 9
} TLIBBusToolDeviceType;
typedef enum _TLIBApplicationChannelType{APP_CAN = 0, APP_LIN = 1, APP_FlexRay = 2, APP_Ethernet = 3} TLIBApplicationChannelType;
typedef enum _TReplayPhase{rppInit = 0, rppReplaying, rppEnded} TReplayPhase;
typedef enum _TLIBCANBusStatistics{
    cbsBusLoad = 0, cbsPeakLoad, cbsFpsStdData, cbsAllStdData,
    cbsFpsExtData, cbsAllExtData, cbsFpsStdRemote, cbsAllStdRemote,
    cbsFpsExtRemote, cbsAllExtRemote, cbsFpsErrorFrame, cbsAllErrorFrame    
} TLIBCANBusStatistics;
typedef struct _TLIBHWInfo{
    TLIBBusToolDeviceType FDeviceType;
    s32 FDeviceIndex;
    char FVendorName[32];
    char FDeviceName[32];
    char FSerialString[64];
} TLIBHWInfo, *PLIBHWInfo;
struct _TLIBTSMapping {
    char                       FAppName[APP_DEVICE_NAME_LENGTH];
    s32                        FAppChannelIndex;
    TLIBApplicationChannelType FAppChannelType;
    TLIBBusToolDeviceType      FHWDeviceType;
    s32                        FHWIndex;
    s32                        FHWChannelIndex;
    s32                        FHWDeviceSubType;
    char                       FHWDeviceName[APP_DEVICE_NAME_LENGTH];
    bool                       FMappingDisabled;
    void init(void) {
        s32 i;
        for (i = 0; i < APP_DEVICE_NAME_LENGTH; i++) {
            FAppName[i] = 0;
            FHWDeviceName[i] = 0;
        }
        FAppChannelIndex = 0;
        FAppChannelType = APP_CAN;
        FHWDeviceType = TS_USB_DEVICE;
        FHWIndex = 0;
        FHWChannelIndex = 0;
        FHWDeviceSubType = 0;
        FMappingDisabled = false;
    }
};
typedef struct _TLIBTSMapping TLIBTSMapping, * PLIBTSMapping;
// system var def
typedef enum _TLIBSystemVarType{svtInt32 = 0, svtUInt32, svtInt64, svtUInt64, svtUInt8Array,
    svtInt32Array, svtInt64Array, svtDouble, svtDoubleArray, svtString} TLIBSystemVarType;
typedef struct {
    char              FName[APP_DEVICE_NAME_LENGTH];
    char              FCategory[APP_DEVICE_NAME_LENGTH];
    char              FComment[APP_DEVICE_NAME_LENGTH];
    TLIBSystemVarType FDataType;
    bool              FIsReadOnly;
    double            FValueMin;
    double            FValueMax;
    char              FUnit[APP_DEVICE_NAME_LENGTH];
} TLIBSystemVarDef, *PLIBSystemVarDef;
typedef enum _TCANFDControllerType{fdtCAN = 0, fdtISOCANFD = 1, fdtNonISOCANFD = 2} TCANFDControllerType;
typedef enum _TCANFDControllerMode{fdmNormal = 0, fdmACKOff = 1, fdmRestricted = 2} TCANFDControllerMode;
// log def
typedef enum _TLIBOnlineReplayTimingMode{ortImmediately = 0, ortAsLog = 1, ortDelayed = 2} TLIBOnlineReplayTimingMode;
typedef enum _TLIBOnlineReplayStatus{orsNotStarted = 0, orsRunning = 1, orsPaused = 2, orsCompleted = 3, orsTerminated = 4} TLIBOnlineReplayStatus;
typedef enum _TSupportedBLFObjType {sotCAN = 0, sotLIN = 1, sotCANFD = 2, sotRealtimeComment = 3, sotSystemVar = 4, sotFlexRay = 5, sotEthernet = 6} TSupportedBLFObjType;
// database utilities
#define DATABASE_STR_LEN 512
// CAN signal record, size = 26
typedef struct _TCANSignal{
    u8     FCANSgnType; // 0 - Unsigned, 1 - Signed, 2 - Single 32, 3 - Double 64
    bool   FIsIntel;
    s32    FStartBit;
    s32    FLength;    
    double FFactor;
    double FOffset;    
} TCANSignal, *PCANSignal;
// LIN signal record, size = 26
typedef struct _TLINSignal{
    u8     FLINSgnType; // 0 - Unsigned, 1 - Signed, 2 - Single 32, 3 - Double 64
    bool   FIsIntel;
    s32    FStartBit;
    s32    FLength;    
    double FFactor;
    double FOffset;    
} TLINSignal, *PLINSignal;
// FlexRay signal record, size = 32
typedef struct _TFlexRaySignal{
    u8     FFRSgnType;   // 0 - Unsigned, 1 - Signed, 2 - Single 32, 3 - Double 64
    u8     FCompuMethod; // 0 - Identical, 1 - Linear, 2 - Scale Linear, 3 - TextTable, 4 - TABNoIntp, 5 - Formula
    u8     FReserved;
    bool   FIsIntel;
    s32    FStartBit;
    s32    FUpdateBit;
    s32    FLength;
    double FFactor;
    double FOffset;
    s32    FActualStartBit;
    s32    FActualUpdateBit;
} TFlexRaySignal, *PFlexRaySignal;
#define CANMsgDecl(typ, name, chn, prop, dlc, id) const typ name = {{chn, prop, MIN(8, dlc), 0, id, 0, {0}}};
#define CANFDMsgDecl(typ, name, chn, prop, dlc, id) const typ name = {{chn, prop, MIN(15, dlc), 1, id, 0, {0}}};
#define FlexRayFrameDecl(typ, name, chn, chnmask, prop, dlc, cycle, slot) const typ name = {{chn, chnmask, 0, MIN(254, dlc), MIN(254, dlc), cycle, 5, 0, 0, 0, 0, slot, prop, 0, 0, 0, 0, {0}}};
#define LINMsgDecl(typ, name, chn, prop, dlc, id) const typ name = {{chn, 0, prop, MIN(8, dlc), id, 0, 0, 0, {0}}};
#define CANSgnDecl(name, typ, isIntel, startBit, len, factor, offset) const TCANSignal name = {typ, isIntel, startBit, len, factor, offset};
#define LINSgnDecl(name, typ, isIntel, startBit, len, factor, offset) const TLINSignal name = {typ, isIntel, startBit, len, factor, offset};
#define FlexRaySgnDecl(name, typ, isIntel, compuMethod, startBit, updateBit, len, factor, offset, actualStartBit, actualUpdateBit) const TFlexRaySignal name = {typ, compuMethod, 0, isIntel, startBit, updateBit, len, factor, offset, actualStartBit, actualUpdateBit};
typedef enum _TSignalType {stCANSignal, stLINSignal, stSystemVar, stFlexRay, stEthernet} TSignalType;
typedef enum _TSignalCheckKind {sckAlways, sckAppear, sckStatistics, sckRisingEdge, sckFallingEdge, sckMonotonyRising, sckMonotonyFalling, sckFollow, sckJump, sckNoChange} TSignalCheckKind;
typedef enum _TSignalStatisticsKind {sskMin, sskMax, sskAverage, sskStdDeviation} TSignalStatisticsKind;
typedef enum _TLIBRBSInitValueOptions{rivUseDB = 0, rivUseLast, rivUse0} TLIBRBSInitValueOptions;
typedef enum _TSymbolMappingDirection{smdBiDirection = 0, smdSgnToSysVar, smdSysVarToSgn} TSymbolMappingDirection;
typedef void(__stdcall* TProgressCallback)(const void* AObj, const double AProgress100);
typedef bool(__stdcall* TCheckResultCallback)(void);
// TDBProperties for database properties, size = 1056
typedef struct _TDBProperties {
    s32 FDBIndex;
    s32 FSignalCount;
    s32 FFrameCount;
    s32 FECUCount;
    u64 FSupportedChannelMask;
    char FName[DATABASE_STR_LEN];
    char FComment[DATABASE_STR_LEN];
    u32  FFlags;
    u32  FDBId;
} TDBProperties, *PDBProperties;
// TDBECUProperties for database ECU properties, size = 1040
typedef struct _TDBECUProperties {
    s32 FDBIndex;
    s32 FECUIndex;
    s32 FTxFrameCount;
    s32 FRxFrameCount;
    char FName[DATABASE_STR_LEN];
    char FComment[DATABASE_STR_LEN];
} TDBECUProperties, *PDBECUProperties;
// TDBFrameProperties for database Frame properties, size = 1088
typedef struct _TDBFrameProperties {
    s32 FDBIndex;
    s32 FECUIndex;
    s32 FFrameIndex;
    u8  FIsTx;    
    u8  FReserved1;
    u16 FCycleTimeMs;
    TSignalType FFrameType;
    // CAN
    u8  FCANIsDataFrame;
    u8  FCANIsStdFrame;
    u8  FCANIsEdl;
    u8  FCANIsBrs;
    s32 FCANIdentifier;
    s32 FCANDLC;
    s32 FCANDataBytes;
    // LIN
    s32 FLINIdentifier;
    s32 FLINDLC;
    // FlexRay
    u8  FFRChannelMask;
    u8  FFRBaseCycle;
    u8  FFRCycleRepetition;
    u8  FFRIsStartupFrame;
    u16 FFRSlotId;  
    u16 FFRDLC;
    u64 FFRCycleMask;
    s32 FSignalCount;
    char FName[DATABASE_STR_LEN];
    char FComment[DATABASE_STR_LEN];
} TDBFrameProperties, *PDBFrameProperties;
// TDBSignalProperties for database signal properties, size = 1144
typedef struct _TDBSignalProperties {
    s32 FDBIndex;
    s32 FECUIndex;
    s32 FFrameIndex;
    s32 FSignalIndex;
    u8  FIsTx;    
    u8  FReserved1;
    u8  FReserved2;
    u8  FReserved3;
    TSignalType    FSignalType;    
    TCANSignal     FCANSignal;
    TLINSignal     FLINSignal;
    TFlexRaySignal FFlexRaySignal;
    s32            FParentFrameId;
    double         FInitValue;
    char FName[DATABASE_STR_LEN];
    char FComment[DATABASE_STR_LEN];
} TDBSignalProperties, *PDBSignalProperties;
// Realtime comment
typedef struct _realtime_comment_t {
    s64 FTimeUs;
    s32 FEventType;
    u32 FCapacity;
    char* FComment;
} Trealtime_comment_t, *Prealtime_comment_t;
// callbacks
typedef void(__cdecl* TCProcedure)(void); 
typedef void(__stdcall* TOnRpcData)(const pu8 AAddr, const native_int ASize);
typedef void (__stdcall* TOnAutoSARE2ECanEvt)(const PCANFD ACAN, const u32 ADataId, pu64 AValue);
typedef void (__stdcall* TOnUSBPlugEvent)(const char* AVidPid, const char* ASerial);
// Sys Var
typedef void(__stdcall* TOnSysVarChange)(const char* ACompleteName);
// IP
typedef void(__stdcall* TOnIoIPData)(pu8 APointer, s32 ASize);
typedef void(__stdcall* TOnIoIPConnection)(const char* AIPAddress, const s32 APort);
typedef enum _TUDPFragmentProcessStatus {ufpsNotFragment, ufpsInvalid, ufpsProcessing, ufpsDone} TUDPFragmentProcessStatus, *PUDPFragmentProcessStatus;
// PDU
typedef void(__stdcall* TOnAutoSARPDUQueueEvent)(const s32 AChnIdx, const char* APDUName, const u64 ATimestamp, const u8 AIsTx, const u32 AID, const u32 ADataLength, const pu8 AData);
typedef s32(__stdcall* TOnAutoSARPDUPreTxEvent)(const s32 AChnIdx, const char* APDUName, const u32 AID, const u32 ASrcDataLength, const pu8 ASrcData, const pu32 ADestDataLength, const pu8 ADestData);
// Automation Module - Graphic Program
typedef enum _TAutomationModuleRunningState {amrsNotRun, amrsPrepareRun, amrsRunning, amrsPaused, amrsStepping, amrsFinished} TAutomationModuleRunningState, *PAutomationModuleRunningState;
typedef enum _TLIBAutomationSignalType {lastCANSignal, lastLINSignal, lastSysVar, lastLocalVar, lastConst, lastFlexRaySignal, lastImmediateValue} TLIBAutomationSignalType, *PLIBAutomationSignalType;
typedef enum _TSignalTesterFailReason {
    tfrNoError = 0,
    tfrCheckSignalNotExistsInDB,
    tfrMinBiggerThanMax,
    tfrStartTimeBiggerThanEndTime,
    tfrTriggerMinBiggerThanMax,
    tfrSignalCountIs0,
    tfrFollowSignalNotExistsInDB,
    tfrTriggerSignalNotExistsInDB,
    tfrSignalFollowViolation,
    tfrSignalMonotonyRisingViolation,
    tfrSignalMonotonyFallingViolation,
    tfrSignalNoChangeViolation,
    tfrSignalValueOutOfRange,
    tfrCANSignalNotExists,
    tfrLINSignalNotExists,
    tfrFlexRaySignalNotExists,
    tfrSystemVarNotExists,
    tfrSignalTesterStartFailedDueToInvalidConf,
    tfrSignalValueNotExists,
    tfrStatisticsCheckViolation,
    tfrTriggerValueNotExists,
    tfrFollowValueNotExists,
    tfrTriggerValueNeverInRange,
    tfrTimeRangeNotTouched,
    tfrRisingNotDetected,
    tfrFallingNotDetected,
    tfrNotAppeared,
    tfrJumpNotDetected
} TSignalTesterFailReason, *PSignalTesterFailReason;
typedef enum _TLIBMPFuncSource {lmfsSystemFunc, lmfsMPLib, lmfsInternal} TLIBMPFuncSource;
typedef enum _TLIBSimVarType {lvtInteger, lvtDouble, lvtString, lvtCANMsg, lvtCANFDMsg, lvtLINMsg} TLIBSimVarType;
// stim
typedef enum _TSTIMSignalStatus {sssStopped, sssRunning, sssPaused} TSTIMSignalStatus, *PSTIMSignalStatus;
// UI Panel
typedef enum _TLIBPanelSignalType {pstNone, pstCANSignal, pstLINSignal, pstSystemVar, pstFlexRaySignal, pstAPICall} TLIBPanelSignalType, *PLIBPanelSignalType;
typedef enum _TLIBPanelControlType {
    pctText,             // Text
    pctImage,            // Image
    pctGroupBox,         // Group Box
    pctPanel,            // Container
    pctPathButton,       // Path Button
    pctCheckBox,         // Check Box
    pctTrackBar,         // Track Bar
    pctScrollBar,        // Scroll Bar
    pctInputOutputBox,   // Input Output Box
    pctImageButton,      // Image Button
    pctSelector,         // Selector
    pctButton,           // Button
    pctProgressBar,      // Progress Bar
    pctRadioButton,      // Radio Button
    pctStartStopButton,  // Start Stop Button
    pctSwitch,           // Switch
    pctLED,              // LED
    pctPageControl,      // Page Control
    pctGauge,            // Gauge
    pctGraphics,         // Graphics
    pctPie,              // Pie
    pctRelationChart,    // Relation Chart
    pctMemo,             // Memo
    pctScrollBox,        // Scroll Box
} TLIBPanelControlType, *PLIBPanelControlType;

// =========================== APP ===========================
typedef s32 (__stdcall* TTSAppSetCurrentApplication)(const char* AAppName);
typedef s32 (__stdcall* TTSAppGetCurrentApplication)(char** AAppName);
typedef s32 (__stdcall* TTSAppDelApplication)(const char* AAppName);
typedef s32 (__stdcall* TTSAppAddApplication)(const char* AAppName);
typedef s32 (__stdcall* TTSAppGetApplicationList)(char** AAppNameList);
typedef s32 (__stdcall* TTSAppSetCANChannelCount)(const s32 ACount);
typedef s32 (__stdcall* TTSAppSetLINChannelCount)(const s32 ACount);
typedef s32 (__stdcall* TTSAppGetCANChannelCount)(const ps32 ACount);
typedef s32 (__stdcall* TTSAppGetLINChannelCount)(const ps32 ACount);
typedef s32 (__stdcall* TTSAppGetFlexRayChannelCount)(const ps32 ACount);
typedef s32 (__stdcall* TTSAppSetFlexRayChannelCount)(const s32 ACount);
typedef s32 (__stdcall* TTSAppSetMapping)(const PLIBTSMapping AMapping);
typedef s32 (__stdcall* TTSAppGetMapping)(const PLIBTSMapping AMapping);
typedef s32 (__stdcall* TTSAppDeleteMapping)(const PLIBTSMapping AMapping);
typedef s32 (__stdcall* TTSAppConnectApplication)(void);
typedef s32 (__stdcall* TTSAppDisconnectApplication)(const void* AObj);
typedef s32 (__stdcall* TTSAppIsConnected)(void);
typedef s32 (__stdcall* TTSAppLogger)(const char* AStr, const TLogLevel ALevel);
typedef s32 (__stdcall* TTSDebugLog)(const void* AObj, const char* AFile, const char* AFunc, const s32 ALine, const char* AStr, const TLogLevel ALevel);
typedef s32 (__stdcall* TTSAppSetTurboMode)(const bool AEnable);
typedef s32 (__stdcall* TTSAppGetTurboMode)(const bool* AEnable);
typedef s32 (__stdcall* TTSAppGetErrorDescription)(const s32 ACode, char** ADesc);
typedef s32 (__stdcall* TTSAppConfigureBaudrateCAN)(const s32 AIdxChn, const float ABaudrateKbps, const bool AListenOnly, const bool AInstallTermResistor120Ohm);
typedef s32 (__stdcall* TTSAppConfigureBaudrateCANFD)(const s32 AIdxChn, const float ABaudrateArbKbps, const float ABaudrateDataKbps, const TCANFDControllerType AControllerType, const TCANFDControllerMode AControllerMode, const bool AInstallTermResistor120Ohm);
typedef s32 (__stdcall* TTSAppTerminate)(const void* AObj);
typedef s32 (__stdcall* TTSWaitTime)(const void* AObj, const s32 ATimeMs, const char* AMsg);
typedef s32 (__stdcall* TTSCheckError)(const void* AObj, const s32 AErrorCode);
typedef s32 (__stdcall* TTSStartLog)(const void* AObj);
typedef s32 (__stdcall* TTSEndLog)(const void* AObj);
typedef s32 (__stdcall* TTSCheckTerminate)(const void* AObj);
typedef s32 (__stdcall* TTSGetTimestampUs)(s64* ATimestamp);
typedef s32 (__stdcall* TTSShowConfirmDialog)(const char* ATitle, const char* APrompt, const char* AImage, const s32 ATimeoutMs, const bool ADefaultOK);
typedef s32 (__stdcall* TTSPause)(void);
typedef s32 (__stdcall* TTSSetCheckFailedTerminate)(const void* AObj, const s32 AToTerminate);
typedef s32 (__stdcall* TTSAppSplitString)(const char* ASplitter, const char* AStr, char** AArray, const s32 ASingleStrSize, const s32 AArraySize, s32* AActualCount);
typedef s32 (__stdcall* TTSAppGetConfigurationFileName)(char** AFileName);
typedef s32 (__stdcall* TTSAppGetConfigurationFilePath)(char** AFilePath);
typedef s32 (__stdcall* TTSAppSetDefaultOutputDir)(const char* APath);
typedef s32 (__stdcall* TTSAppSaveScreenshot)(const char* AFormCaption, const char* AFilePath);
typedef s32 (__stdcall* TTSAppRunForm)(const char* AFormCaption);
typedef s32 (__stdcall* TTSAppStopForm)(const char* AFormCaption);
typedef s32 (__stdcall* TClearMeasurementForm)(const char* AFormCaption);
// system var def
typedef s32 (__stdcall* TTSAppGetSystemVarCount)(s32* AInternalCount, s32* AUserCount);
typedef s32 (__stdcall* TTSAppGetSystemVarDefByIndex)(const bool AIsUser, const s32 AIndex, const PLIBSystemVarDef AVarDef);
typedef s32 (__stdcall* TTSAppFindSystemVarDefByName)(const bool AIsUser, const char* ACompleteName, const PLIBSystemVarDef AVarDef);
typedef s32 (__stdcall* TTSAppCreateSystemVar)(const char* ACompleteName, const TLIBSystemVarType AType, const char* ADefaultValue, const char* AComment);
typedef s32 (__stdcall* TTSAppDeleteSystemVar)(const char* ACompleteName);
typedef s32 (__stdcall* TTSAppSetSystemVarUnit)(const char* ACompleteName, const char* AUnit);
typedef s32 (__stdcall* TTSAppSetSystemVarValueTable)(const char* ACompleteName, const char* ATable);
typedef s32 (__stdcall* TTSAppGetSystemVarAddress)(const char* ACompleteName, pnative_int AAddress);
typedef s32 (__stdcall* TTSAppSetSystemVarLogging)(const char* ACompleteName, const bool AIsLogging);
typedef s32 (__stdcall* TTSAppGetSystemVarLogging)(const char* ACompleteName, bool* AIsLogging);
typedef s32 (__stdcall* TTSAppLogSystemVarValue)(const void* AObj, const char* ACompleteName);
// system var get
typedef s32 (__stdcall* TTSAppGetSystemVarDouble)(const char* ACompleteName, double* AValue);
typedef s32 (__stdcall* TTSAppGetSystemVarInt32)(const char* ACompleteName, s32* AValue);
typedef s32 (__stdcall* TTSAppGetSystemVarUInt32)(const char* ACompleteName, u32* AValue);
typedef s32 (__stdcall* TTSAppGetSystemVarInt64)(const char* ACompleteName, s64* AValue);
typedef s32 (__stdcall* TTSAppGetSystemVarUInt64)(const char* ACompleteName, u64* AValue);
typedef s32 (__stdcall* TTSAppGetSystemVarUInt8Array)(const char* ACompleteName, const s32 AValueCapacity, s32* AVarCount, u8* AValue);
typedef s32 (__stdcall* TTSAppGetSystemVarInt32Array)(const char* ACompleteName, const s32 AValueCapacity, s32* AVarCount, s32* AValue);
typedef s32 (__stdcall* TTSAppGetSystemVarInt64Array)(const char* ACompleteName, const s32 AValueCapacity, s32* AVarCount, s64* AValue);
typedef s32 (__stdcall* TTSAppGetSystemVarDoubleArray)(const char* ACompleteName, const s32 AValueCapacity, s32* AVarCount, double* AValue);
typedef s32 (__stdcall* TTSAppGetSystemVarString)(const char* ACompleteName, const s32 AValueCapacity, char* AString);
typedef s32 (__stdcall* TTSAppGetSystemVarGerneric)(const char* ACompleteName, const s32 AValueCapacity, char* AValue);
typedef s32 (__stdcall* TTSWaitSystemVariable)(const char* ACompleteName, const char* AValue, const s32 ATimeoutMs);
// system var sync set
typedef s32 (__stdcall* TTSAppSetSystemVarDouble)(const char* ACompleteName, const double AValue);
typedef s32 (__stdcall* TTSAppSetSystemVarInt32)(const char* ACompleteName, const s32 AValue);
typedef s32 (__stdcall* TTSAppSetSystemVarUInt32)(const char* ACompleteName, const u32 AValue);
typedef s32 (__stdcall* TTSAppSetSystemVarInt64)(const char* ACompleteName, const s64 AValue);
typedef s32 (__stdcall* TTSAppSetSystemVarUInt64)(const char* ACompleteName, const u64 AValue);
typedef s32 (__stdcall* TTSAppSetSystemVarUInt8Array)(const char* ACompleteName, const s32 ACount, const u8* AValue);
typedef s32 (__stdcall* TTSAppSetSystemVarInt32Array)(const char* ACompleteName, const s32 ACount, const s32* AValue);
typedef s32 (__stdcall* TTSAppSetSystemVarInt64Array)(const char* ACompleteName, const s32 ACount, const s64* AValue);
typedef s32 (__stdcall* TTSAppSetSystemVarDoubleArray)(const char* ACompleteName, const s32 ACount, const double* AValue);
typedef s32 (__stdcall* TTSAppSetSystemVarString)(const char* ACompleteName, const char* AString);
typedef s32 (__stdcall* TTSAppSetSystemVarGeneric)(const char* ACompleteName, const char* AValue);
// system var async set
typedef s32 (__stdcall* TTSAppSetSystemVarDoubleAsync)(const char* ACompleteName, const double AValue);
typedef s32 (__stdcall* TTSAppSetSystemVarInt32Async)(const char* ACompleteName, const s32 AValue);
typedef s32 (__stdcall* TTSAppSetSystemVarUInt32Async)(const char* ACompleteName, const u32 AValue);
typedef s32 (__stdcall* TTSAppSetSystemVarInt64Async)(const char* ACompleteName, const s64 AValue);
typedef s32 (__stdcall* TTSAppSetSystemVarUInt64Async)(const char* ACompleteName, const u64 AValue);
typedef s32 (__stdcall* TTSAppSetSystemVarUInt8ArrayAsync)(const char* ACompleteName, const s32 ACount, const u8* AValue);
typedef s32 (__stdcall* TTSAppSetSystemVarInt32ArrayAsync)(const char* ACompleteName, const s32 ACount, const s32* AValue);
typedef s32 (__stdcall* TTSAppSetSystemVarInt64ArrayAsync)(const char* ACompleteName, const s32 ACount, const s64* AValue);
typedef s32 (__stdcall* TTSAppSetSystemVarDoubleArrayAsync)(const char* ACompleteName, const s32 ACount, const double* AValue);
typedef s32 (__stdcall* TTSAppSetSystemVarStringAsync)(const char* ACompleteName, const char* AString);
typedef s32 (__stdcall* TTSAppSetSystemVarGenericAsync)(const char* ACompleteName, const char* AValue);
// system var utils
typedef s32 (__stdcall* TTSAppLogSystemVar)(const char* ACompleteName);
typedef s32 (__stdcall* TTSAppWaitSystemVarExistance)(const char* ACompleteName, const s32 ATimeOutMs);
typedef s32 (__stdcall* TTSAppWaitSystemVarDisappear)(const char* ACompleteName, const s32 ATimeOutMs);
// excel
typedef s32 (__stdcall* Texcel_load)(const char* AFileName, void** AObj);
typedef s32 (__stdcall* Texcel_get_sheet_count)(const void* AObj, s32* ACount);
typedef s32 (__stdcall* Texcel_set_sheet_count)(const void* AObj, const s32 ACount);
typedef s32 (__stdcall* Texcel_get_sheet_name)(const void* AObj, const s32 AIdxSheet, char** AName);
typedef s32 (__stdcall* Texcel_set_sheet_name)(const void* AObj, const s32 AIdxSheet, const char* AName);
typedef s32 (__stdcall* Texcel_get_cell_count)(const void* AObj, const s32 AIdxSheet, s32* ARowCount, s32* AColCount);
typedef s32 (__stdcall* Texcel_get_cell_value)(const void* AObj, const s32 AIdxSheet, const s32 AIdxRow, const s32 AIdxCol, char** AValue);
typedef s32 (__stdcall* Texcel_set_cell_count)(const void* AObj, const s32 AIdxSheet, const s32 ARowCount, const s32 AColCount);
typedef s32 (__stdcall* Texcel_set_cell_value)(const void* AObj, const s32 AIdxSheet, const s32 AIdxRow, const s32 AIdxCol, char* AValue);
typedef s32 (__stdcall* Texcel_unload)(const void* AObj);
typedef s32 (__stdcall* Texcel_unload_all)(void);
// text file write
typedef s32 (__stdcall* TWriteTextFileStart)(const char* AFileName, native_int* AHandle);
typedef s32 (__stdcall* TWriteTextFileLine)(const native_int AHandle, const char* ALine);
typedef s32 (__stdcall* TWriteTextFileLineWithDoubleArray)(const native_int AHandle, const double* AArray, const s32 ACount);
typedef s32 (__stdcall* TWriteTextFileLineWithStringArray)(const native_int AHandle, const char** AArray, const s32 ACount);
typedef s32 (__stdcall* TWriteTextFileEnd)(const native_int AHandle);
// text file read
typedef s32 (__stdcall* TReadTextFileStart)(const char* AFileName, native_int* AHandle);
typedef s32 (__stdcall* TReadTextFileLine)(const native_int AHandle, const s32 ALineCapacity, ps32 AReadCharCount, char* ALine);
typedef s32 (__stdcall* TReadTextFileEnd)(const native_int AHandle);
// mat file
typedef s32 (__stdcall* TWriteMatFileStart)(const char* AFileName, native_int* AHandle);
typedef s32 (__stdcall* TWriteMatFileVariableDouble)(const native_int AHandle, const char* AVarName, const double AValue);
typedef s32 (__stdcall* TWriteMatFileVariableString)(const native_int AHandle, const char* AVarName, const char* AValue);
typedef s32 (__stdcall* TWriteMatFileVariableDoubleArray)(const native_int AHandle, const char* AVarName, const double* AArray, const s32 ACount);
typedef s32 (__stdcall* TWriteMatFileEnd)(const native_int AHandle);
typedef s32 (__stdcall* TReadMatFileStart)(const char* AFileName, native_int* AHandle);
typedef s32 (__stdcall* TReadMatFileVariableCount)(const native_int AHandle, const char* AVarName, ps32 ACount);
typedef s32 (__stdcall* TReadMatFileVariableString)(const native_int AHandle, const char* AVarName, char* AValue, const s32 AValueCapacity);
typedef s32 (__stdcall* TReadMatFileVariableDouble)(const native_int AHandle, const char* AVarName, const double* AValue, const s32 AStartIdx, const s32 ACount);
typedef s32 (__stdcall* TReadMatFileEnd)(const native_int AHandle);
// ini file
typedef s32 (__stdcall* TIniCreate)(const char* AFileName, native_int* AHandle);
typedef s32 (__stdcall* TIniWriteInt32)(const native_int AHandle, const char* ASection, const char* AKey, const s32 AValue);
typedef s32 (__stdcall* TIniWriteInt64)(const native_int AHandle, const char* ASection, const char* AKey, const s64 AValue);
typedef s32 (__stdcall* TIniWriteBool)(const native_int AHandle, const char* ASection, const char* AKey, const bool AValue);
typedef s32 (__stdcall* TIniWriteFloat)(const native_int AHandle, const char* ASection, const char* AKey, const double AValue);
typedef s32 (__stdcall* TIniWriteString)(const native_int AHandle, const char* ASection, const char* AKey, const char* AValue);
typedef s32 (__stdcall* TIniReadInt32)(const native_int AHandle, const char* ASection, const char* AKey, const s32* AValue, const s32 ADefault);
typedef s32 (__stdcall* TIniReadInt64)(const native_int AHandle, const char* ASection, const char* AKey, const s64* AValue, const s64 ADefault);
typedef s32 (__stdcall* TIniReadBool)(const native_int AHandle, const char* ASection, const char* AKey, const bool* AValue, const bool ADefault);
typedef s32 (__stdcall* TIniReadFloat)(const native_int AHandle, const char* ASection, const char* AKey, const double* AValue, const double ADefault);
typedef s32 (__stdcall* TIniReadString)(const native_int AHandle, const char* ASection, const char* AKey, const char* AValue, s32* AValueCapacity, const char* ADefault);
typedef s32 (__stdcall* TIniSectionExists)(const native_int AHandle, const char* ASection);
typedef s32 (__stdcall* TIniKeyExists)(const native_int AHandle, const char* ASection, const char* AKey);
typedef s32 (__stdcall* TIniDeleteKey)(const native_int AHandle, const char* ASection, const char* AKey);
typedef s32 (__stdcall* TIniDeleteSection)(const native_int AHandle, const char* ASection);
typedef s32 (__stdcall* TIniClose)(const native_int AHandle);
// automation module - Graphic Program
typedef s32 (__stdcall* TAMGetRunningState)(const char* AModuleName, PAutomationModuleRunningState AState, char** ASubModuleName, char** ACurrentParameterGroupName);
typedef s32 (__stdcall* TAMRun)(const char* AModuleName, const char* ASubModuleName, const char* AParameterGroupName, const bool AIsSync);
typedef s32 (__stdcall* TAMStop)(const char* AModuleName, const bool AIsSync);
typedef s32 (__stdcall* TAMSelectSubModule)(const bool AIsSelect, const char* AModuleName, const char* ASubModuleName, const char* AParameterGroupName);
// panel set
typedef s32 (__stdcall* TPanelSetEnable)(const char* APanelName, const char* AControlName, const bool AEnable);
typedef s32 (__stdcall* TPanelSetPositionX)(const char* APanelName, const char* AControlName, const float AX);
typedef s32 (__stdcall* TPanelSetPositionY)(const char* APanelName, const char* AControlName, const float AY);
typedef s32 (__stdcall* TPanelSetPositionXY)(const char* APanelName, const char* AControlName, const float AX, const float AY);
typedef s32 (__stdcall* TPanelSetOpacity)(const char* APanelName, const char* AControlName, const float AOpacity);
typedef s32 (__stdcall* TPanelSetWidth)(const char* APanelName, const char* AControlName, const float AWidth);
typedef s32 (__stdcall* TPanelSetHeight)(const char* APanelName, const char* AControlName, const float AHeight);
typedef s32 (__stdcall* TPanelSetWidthHeight)(const char* APanelName, const char* AControlName, const float AWidth, const float AHeight);
typedef s32 (__stdcall* TPanelSetRotationAngle)(const char* APanelName, const char* AControlName, const float AAngleDegree);
typedef s32 (__stdcall* TPanelSetRotationCenter)(const char* APanelName, const char* AControlName, const float ARatioX, const float ARatioY);
typedef s32 (__stdcall* TPanelSetScaleX)(const char* APanelName, const char* AControlName, const float AScaleX);
typedef s32 (__stdcall* TPanelSetScaleY)(const char* APanelName, const char* AControlName, const float AScaleY);
typedef s32 (__stdcall* TPanelSetBkgdColor)(const char* APanelName, const char* AControlName, const u32 AAlphaColor);
typedef s32 (__stdcall* TPanelSetSelectorItems)(const char* APanelName, const char* AControlName, const char* AItemsList);
// panel get
typedef s32 (__stdcall* TPanelGetEnable)(const char* APanelName, const char* AControlName, bool* AEnable);
typedef s32 (__stdcall* TPanelGetPositionXY)(const char* APanelName, const char* AControlName, float* AX, float* AY);
typedef s32 (__stdcall* TPanelGetOpacity)(const char* APanelName, const char* AControlName, float* AOpacity);
typedef s32 (__stdcall* TPanelGetWidthHeight)(const char* APanelName, const char* AControlName, float* AWidth, float* AHeight);
typedef s32 (__stdcall* TPanelGetRotationAngle)(const char* APanelName, const char* AControlName, float* AAngleDegree);
typedef s32 (__stdcall* TPanelGetRotationCenter)(const char* APanelName, const char* AControlName, float* ARatioX, float* ARatioY);
typedef s32 (__stdcall* TPanelGetScaleXY)(const char* APanelName, const char* AControlName, float* AScaleX, float* AScaleY);
typedef s32 (__stdcall* TPanelGetBkgdColor)(const char* APanelName, const char* AControlName, pu32 AAlphaColor);
typedef s32 (__stdcall* TPanelGetSelectorItems)(const char* APanelName, const char* AControlName, char** AItemsList);
// stim
typedef s32 (__stdcall* TSTIMSetSignalStatus)(const char* ASTIMName, const char* AUserLabel, TSTIMSignalStatus AStatus);
typedef s32 (__stdcall* TSTIMGetSignalStatus)(const char* ASTIMName, const char* AUserLabel, PSTIMSignalStatus AStatus);
// Atomic
typedef s32 (__stdcall* TAtomicIncrement32)(const ps32 AAddr, const s32 AValue, ps32 AResult);
typedef s32 (__stdcall* TAtomicIncrement64)(const ps64 AAddr, const s64 AValue, ps64 AResult);
typedef s32 (__stdcall* TAtomicSet32)(const ps32 AAddr, const s32 AValue);
typedef s32 (__stdcall* TAtomicSet64)(const ps64 AAddr, const s64 AValue);
// symbol mapping
typedef s32 (__stdcall* TAddDirectMappingCAN)(const char* ADestinationVarName, const char* ASignalAddress, const TSymbolMappingDirection ADirection);
typedef s32 (__stdcall* TAddDirectMappingWithFactorOffsetCAN)(const char* ADestinationVarName, const char* ASignalAddress, const TSymbolMappingDirection ADirection, const double AFactor, const double AOffset);
typedef s32 (__stdcall* TAddExpressionMapping)(const char* ADestinationVarName, const char* AExpression, const char* AArguments);
typedef s32 (__stdcall* TDeleteSymbolMappingItem)(const char* ADestinationVarName);
typedef s32 (__stdcall* TDeleteSymbolMappingItems)(void);
typedef s32 (__stdcall* TEnableSymbolMappingItem)(const char* ADestinationVarName, const bool AEnable);
typedef s32 (__stdcall* TEnableSymbolMappingEngine)(const bool AEnable);
typedef s32 (__stdcall* TSaveSymbolMappingSettings)(const char* AFileName);
typedef s32 (__stdcall* TLoadSymbolMappingSettings)(const char* AFileName);
// database
typedef s32 (__stdcall* TDBGetCANDBCount)(ps32 ACount);
typedef s32 (__stdcall* TDBGetLINDBCount)(ps32 ACount);
typedef s32 (__stdcall* TDBGetFlexRayDBCount)(ps32 ACount);
typedef s32 (__stdcall* TDBGetCANDBPropertiesByIndex)(PDBProperties AValue);
typedef s32 (__stdcall* TDBGetLINDBPropertiesByIndex)(PDBProperties AValue);
typedef s32 (__stdcall* TDBGetFlexRayDBPropertiesByIndex)(PDBProperties AValue);
typedef s32 (__stdcall* TDBGetCANDBECUPropertiesByIndex)(PDBECUProperties AValue);
typedef s32 (__stdcall* TDBGetLINDBECUPropertiesByIndex)(PDBECUProperties AValue);
typedef s32 (__stdcall* TDBGetFlexRayDBECUPropertiesByIndex)(PDBECUProperties AValue);
typedef s32 (__stdcall* TDBGetCANDBFramePropertiesByIndex)(PDBFrameProperties AValue);
typedef s32 (__stdcall* TDBGetLINDBFramePropertiesByIndex)(PDBFrameProperties AValue);
typedef s32 (__stdcall* TDBGetFlexRayDBFramePropertiesByIndex)(PDBFrameProperties AValue);
typedef s32 (__stdcall* TDBGetCANDBSignalPropertiesByIndex)(PDBSignalProperties AValue);
typedef s32 (__stdcall* TDBGetLINDBSignalPropertiesByIndex)(PDBSignalProperties AValue);
typedef s32 (__stdcall* TDBGetFlexRayDBSignalPropertiesByIndex)(PDBSignalProperties AValue);
typedef s32 (__stdcall* TDBGetCANDBPropertiesByAddress)(const char* AAddr, PDBProperties AValue);
typedef s32 (__stdcall* TDBGetLINDBPropertiesByAddress)(const char* AAddr, PDBProperties AValue);
typedef s32 (__stdcall* TDBGetFlexRayDBPropertiesByAddress)(const char* AAddr, PDBProperties AValue);
typedef s32 (__stdcall* TDBGetCANDBECUPropertiesByAddress)(const char* AAddr, PDBECUProperties AValue);
typedef s32 (__stdcall* TDBGetLINDBECUPropertiesByAddress)(const char* AAddr, PDBECUProperties AValue);
typedef s32 (__stdcall* TDBGetFlexRayDBECUPropertiesByAddress)(const char* AAddr, PDBECUProperties AValue);
typedef s32 (__stdcall* TDBGetCANDBFramePropertiesByAddress)(const char* AAddr, PDBFrameProperties AValue);
typedef s32 (__stdcall* TDBGetLINDBFramePropertiesByAddress)(const char* AAddr, PDBFrameProperties AValue);
typedef s32 (__stdcall* TDBGetFlexRayDBFramePropertiesByAddress)(const char* AAddr, PDBFrameProperties AValue);
typedef s32 (__stdcall* TDBGetCANDBSignalPropertiesByAddress)(const char* AAddr, PDBSignalProperties AValue);
typedef s32 (__stdcall* TDBGetLINDBSignalPropertiesByAddress)(const char* AAddr, PDBSignalProperties AValue);
typedef s32 (__stdcall* TDBGetFlexRayDBSignalPropertiesByAddress)(const char* AAddr, PDBSignalProperties AValue);
typedef s32 (__stdcall* TDBGetCANDBFramePropertiesByDBIndex)(const s32 AIdxDB, const s32 AIndex, PDBFrameProperties AValue);
typedef s32 (__stdcall* TDBGetLINDBFramePropertiesByDBIndex)(const s32 AIdxDB, const s32 AIndex, PDBFrameProperties AValue);
typedef s32 (__stdcall* TDBGetFlexRayDBFramePropertiesByDBIndex)(const s32 AIdxDB, const s32 AIndex, PDBFrameProperties AValue);
typedef s32 (__stdcall* TDBGetCANDBSignalPropertiesByDBIndex)(const s32 AIdxDB, const s32 AIndex, PDBSignalProperties AValue);
typedef s32 (__stdcall* TDBGetLINDBSignalPropertiesByDBIndex)(const s32 AIdxDB, const s32 AIndex, PDBSignalProperties AValue);
typedef s32 (__stdcall* TDBGetFlexRayDBSignalPropertiesByDBIndex)(const s32 AIdxDB, const s32 AIndex, PDBSignalProperties AValue);
typedef s32 (__stdcall* TDBGetCANDBSignalPropertiesByFrameIndex)(const s32 AIdxDB, const s32 AIdxFrame, const s32 ASgnIndexInFrame, PDBSignalProperties AValue);
typedef s32 (__stdcall* TDBGetLINDBSignalPropertiesByFrameIndex)(const s32 AIdxDB, const s32 AIdxFrame, const s32 ASgnIndexInFrame, PDBSignalProperties AValue);
typedef s32 (__stdcall* TDBGetFlexRayDBSignalPropertiesByFrameIndex)(const s32 AIdxDB, const s32 AIdxFrame, const s32 ASgnIndexInFrame, PDBSignalProperties AValue);
// misc
typedef s32 (__stdcall* TTSAppMakeToast)(const char* AString, const TLogLevel ALevel);
typedef s32 (__stdcall* TTSAppMakeToastUntil)(const char* AString, const TLogLevel ALevel, const bool* ACloseCriteria, const bool AUserCanBreak);
typedef s32 (__stdcall* TTSAppMakeToastWithCallback)(const char* AString, const TLogLevel ALevel, const TCheckResultCallback ACallback, const bool AUserCanBreak);
typedef s32 (__stdcall* TTSAppExecutePythonString)(const char* AString, const char* AArguments, const bool AIsSync, const bool AIsX64, char** AResultLog);
typedef s32 (__stdcall* TTSAppExecutePythonScript)(const char* AFilePath, const char* AArguments, const bool AIsSync, const bool AIsX64, char** AResultLog);
typedef s32 (__stdcall* TTSAppExecuteApp)(const char* AAppPath,  const char* AWorkingDir, const char* AParameter, const s32 AWaitTimeMS);
typedef s32 (__stdcall* TTSAppTerminateAppByName)(const char* AImageName);
typedef s32 (__stdcall* TTSAppCallMPAPI)(const char* ALibName, const char* AFuncName, const char* AInParameters, char** AOutParameters);
typedef s32 (__stdcall* TTSAppSetAnalysisTimeRange)(const s64 ATimeStartUs, const s64 ATimeEndUs);
typedef s32 (__stdcall* TTSAppEnableAllGraphics)(const bool AEnable, const char* AExceptCaptions);
typedef s32 (__stdcall* TTSAppGetTSMasterVersion)(ps32 AYear, ps32 AMonth, ps32 ADay, ps32 ABuildNumber);
typedef s32 (__stdcall* TUIShowPageByIndex)(const s32 AIndex);
typedef s32 (__stdcall* TUIShowPageByName)(const char* AName);
typedef s32 (__stdcall* TWriteRealtimeComment)(const void* AObj, const char* AName);
typedef s32 (__stdcall* TTSAppSetThreadPriority)(const void* AObj, const s32 APriority);
typedef s32 (__stdcall* TTSAppForceDirectory)(const char* ADir);
typedef s32 (__stdcall* TTSAppDirectoryExists)(const char* ADir);
typedef s32 (__stdcall* TTSAppOpenDirectoryAndSelectFile)(const char* AFileName);
typedef s32 (__stdcall* TTSMiniDelayCPU)(void);
typedef s32 (__stdcall* TPromptUserInputValue)(const char* APrompt, double* AValue);
typedef s32 (__stdcall* TPromptUserInputString)(const char* APrompt, char* AValue, const s32 AValueCapacity);
typedef s32 (__stdcall* TTSAppGetDocPath)(char** AFilePath);
typedef s32 (__stdcall* TTSAppGetHWIDString)(char** AIDString);
typedef s32 (__stdcall* TTSAppGetHWIDArray)(pu8 AArray8B);
typedef s32 (__stdcall* TPlaySound)(const bool AIsSync, const char* AWaveFileName);
typedef s32 (__stdcall* TUILoadPlugin)(const char* APluginName);
typedef s32 (__stdcall* TUIUnloadPlugin)(const char* APluginName);
typedef s32 (__stdcall* TUIGetMainWindowHandle)(pnative_int AHandle);
typedef s32 (__stdcall* TPrintDeltaTime)(const char* AInfo);
typedef s32 (__stdcall* TGetConstantDouble)(const char* AName, double* AValue);
typedef s32 (__stdcall* TWaitWithDialog)(const void* AObj, const char* ATitle, const char* AMessage, const bool* ApResult, const float* ApProgress100);
typedef s32 (__cdecl* TRunPythonFunction)(const void* AObj, const char* AModuleName, const char* AFuncName, const char* AArgFormat, ...);
typedef char* (__stdcall* TGetCurrentMpName)(const void* AObj);
typedef s32 (__stdcall* TGetSystemConstantCount)(const s32 AIdxType, ps32 ACount);
typedef s32 (__stdcall* TGetSystemConstantValueByIndex)(const s32 AIdxType, const s32 AIdxValue, char** AName, pdouble AValue, char** ADescription);
typedef s32 (__stdcall* TAddSystemConstant)(const char* AName, const double AValue, const char* ADescription);
typedef s32 (__stdcall* TDeleteSystemConstant)(const char* AName);
typedef s32 (__stdcall* TDBGetFlexRayClusterParameters)(const s32 AIdxChn, const pchar AClusterName, PFlexRayClusterParameters AValue);
typedef s32 (__stdcall* TDBGetFlexRayControllerParameters)(const s32 AIdxChn,  pchar AClusterName, const pchar AECUName, PFlexRayControllerParameters AValue);
typedef s32 (__stdcall* TSetSystemVarEventSupport)(const pchar ACompleteName, const bool ASupport);
typedef s32 (__stdcall* TGetSystemVarEventSupport)(const pchar ACompleteName, pbool ASupport);
typedef s32 (__stdcall* TGetDateTime)(ps32 AYear, ps32 AMonth, ps32 ADay, ps32 AHour, ps32 AMinute, ps32 ASecond, ps32 AMilliseconds);
typedef s32 (__stdcall* TGPGDeleteAllModules)(void);
typedef s32 (__stdcall* TGPGCreateModule)(const pchar AProgramName, const pchar ADisplayName, ps64 AModuleId, ps64 AEntryPointId);
typedef s32 (__stdcall* TGPGDeleteModule)(const s64 AModuleId);
typedef s32 (__stdcall* TGPGDeployModule)(const s64 AModuleId, const pchar AGraphicProgramWindowTitle);
typedef s32 (__stdcall* TGPGAddActionDown)(const s64 AModuleId, const s64 AUpperActionId, const pchar ADisplayName, const pchar AComment, ps64 AActionId);
typedef s32 (__stdcall* TGPGAddActionRight)(const s64 AModuleId, const s64 ALeftActionId, const pchar ADisplayName, const pchar AComment, ps64 AActionId);
typedef s32 (__stdcall* TGPGAddGoToDown)(const s64 AModuleId, const s64 AUpperActionId, const pchar ADisplayName, const pchar AComment, const pchar AJumpLabel, ps64 AActionId);
typedef s32 (__stdcall* TGPGAddGoToRight)(const s64 AModuleId, const s64 ALeftActionId, const pchar ADisplayName, const pchar AComment, const pchar AJumpLabel, ps64 AActionId);
typedef s32 (__stdcall* TGPGAddFromDown)(const s64 AModuleId, const s64 AUpperActionId, const pchar ADisplayName, const pchar AComment, const pchar AJumpLabel, ps64 AActionId);
typedef s32 (__stdcall* TGPGAddGroupDown)(const s64 AModuleId, const s64 AUpperActionId, const pchar ADisplayName, const pchar AComment, ps64 AGroupId, ps64 AEntryPointId);
typedef s32 (__stdcall* TGPGAddGroupRight)(const s64 AModuleId, const s64 ALeftActionId, const pchar ADisplayName, const pchar AComment, ps64 AGroupId, ps64 AEntryPointId);
typedef s32 (__stdcall* TGPGDeleteAction)(const s64 AModuleId, const s64 AActionId);
typedef s32 (__stdcall* TGPGSetActionNOP)(const s64 AModuleId, const s64 AActionId);
typedef s32 (__stdcall* TGPGSetActionSignalReadWrite)(const s64 AModuleId, const s64 AActionId);
typedef s32 (__stdcall* TGPGSetActionAPICall)(const s64 AModuleId, const s64 AActionId);
typedef s32 (__stdcall* TGPGSetActionExpression)(const s64 AModuleId, const s64 AActionId);
typedef s32 (__stdcall* TGPGConfigureActionBasic)(const s64 AModuleId, const s64 AActionId, const pchar ADisplayName, const pchar AComment, const s32 ATimeoutMs);
typedef s32 (__stdcall* TGPGConfigureGoTo)(const s64 AModuleId, const s64 AActionId, const pchar ADisplayName, const pchar AComment, const pchar AJumpLabel);
typedef s32 (__stdcall* TGPGConfigureFrom)(const s64 AModuleId, const s64 AActionId, const pchar ADisplayName, const pchar AComment, const pchar AJumpLabel);
typedef s32 (__stdcall* TGPGConfigureNOP)(const s64 AModuleId, const s64 AActionId, const bool ANextDirectionIsDown, const bool AResultOK, const bool AJumpBackIfEnded);
typedef s32 (__stdcall* TGPGConfigureGroup)(const s64 AModuleId, const s64 AActionId, const TLIBAutomationSignalType ARepeatCountType, const pchar ARepeatCountRepr);
typedef s32 (__stdcall* TGPGConfigureSignalReadWriteListClear)(const s64 AModuleId, const s64 AActionId);
typedef s32 (__stdcall* TGPGConfigureSignalWriteListAppend)(const s64 AModuleId, const s64 AActionId, const TLIBAutomationSignalType ADestSignalType, const TLIBAutomationSignalType ASrcSignalType, const pchar ADestSignalExpr, const pchar ASrcSignalExpr, ps32 AItemIndex);
typedef s32 (__stdcall* TGPGConfigureSignalReadListAppend)(s64 AModuleId, s64 AActionId, bool AIsConditionAND, TLIBAutomationSignalType ADestSignalType, TLIBAutomationSignalType AMinSignalType, TLIBAutomationSignalType AMaxSignalType, const pchar ADestSignalExpr, const pchar AMinSignalExpr, const pchar AMaxSignalExpr, ps32 AItemIndex);
typedef s32 (__stdcall* TGPGConfigureAPICallArguments)(const s64 AModuleId, const s64 AActionId, const TLIBMPFuncSource AAPIType, const pchar AAPIName, const PLIBAutomationSignalType AAPIArgTypes, char** AAPIArgNames, char** AAPIArgExprs, const s32 AArraySize);
typedef s32 (__stdcall* TGPGConfigureAPICallResult)(const s64 AModuleId, const s64 AActionId, const bool AIgnoreResult, const TLIBAutomationSignalType ASignalType, const pchar ASignalExpr);
typedef s32 (__stdcall* TGPGConfigureExpression)(const s64 AModuleId, const s64 AActionId, const s32 AxCount, const pchar AExpression, const PLIBAutomationSignalType AArgumentTypes, char** AArgumentExprs, const TLIBAutomationSignalType AResultType, const pchar AResultExpr);
typedef s32 (__stdcall* TGPGAddLocalVar)(const s64 AModuleId, const TLIBSimVarType AType, const pchar AName, const pchar AInitValue, const pchar AComment, ps32 AItemIndex);
typedef s32 (__stdcall* TGPGDeleteLocalVar)(const s64 AModuleId, const s32 AItemIndex);
typedef s32 (__stdcall* TGPGDeleteAllLoalVars)(const s64 AModuleId);
typedef s32 (__stdcall* TGPGDeleteGroupItems)(const s64 AModuleId, const s64 AGroupId);
typedef s32 (__stdcall* TGPGConfigureSignalReadWriteListDelete)(const s64 AModuleId, const s64 AActionId, const s32 AItemIndex);
typedef s32 (__stdcall* TGPGConfigureModule)(const s64 AModuleId, const pchar AProgramName, const pchar ADisplayName, const s32 ARepeatCount, const bool ASelected);
typedef s32 (__stdcall* TUIShowWindow)(const pchar AWindowTitle, const bool AIsShow);
typedef s32 (__stdcall* TUIGraphicsLoadConfiguration)(const pchar AWindowTitle, const pchar AConfigurationName);
typedef s32 (__stdcall* TUIWatchdogEnable)(const bool AEnable);
typedef s32 (__stdcall* TUIWatchdogFeed)(void);
typedef s32 (__stdcall* TAddPathToEnvironment)(const char* APath);
typedef s32 (__stdcall* TDeletePathFromEnvironment)(const char* APath);
typedef s32 (__stdcall* TTSAppSetSystemVarDoubleWTime)(const char* ACompleteName, const double AValue, const s64 ATimeUs);
typedef s32 (__stdcall* TTSAppSetSystemVarInt32WTime)(const char* ACompleteName, const s32 AValue, const s64 ATimeUs);
typedef s32 (__stdcall* TTSAppSetSystemVarUInt32WTime)(const char* ACompleteName, const u32 AValue, const s64 ATimeUs);
typedef s32 (__stdcall* TTSAppSetSystemVarInt64WTime)(const char* ACompleteName, const s64 AValue, const s64 ATimeUs);
typedef s32 (__stdcall* TTSAppSetSystemVarUInt64WTime)(const char* ACompleteName, const u64 AValue, const s64 ATimeUs);
typedef s32 (__stdcall* TTSAppSetSystemVarUInt8ArrayWTime)(const char* ACompleteName, const s32 ACount, const pu8 AValue, const s64 ATimeUs);
typedef s32 (__stdcall* TTSAppSetSystemVarInt32ArrayWTime)(const char* ACompleteName, const s32 ACount, const ps32 AValue, const s64 ATimeUs);
typedef s32 (__stdcall* TTSAppSetSystemVarDoubleArrayWTime)(const char* ACompleteName, const s32 ACount, const double* AValue, const s64 ATimeUs);
typedef s32 (__stdcall* TTSAppSetSystemVarStringWTime)(const char* ACompleteName, const char* AValue, const s64 ATimeUs);
typedef s32 (__stdcall* TTSAppSetSystemVarGenericWTime)(const char* ACompleteName, const char* AValue, const s64 ATimeUs);
typedef s32 (__stdcall* TTSAppSetSystemVarDoubleAsyncWTime)(const char* ACompleteName, const double AValue, const s64 ATimeUs);
typedef s32 (__stdcall* TTSAppSetSystemVarInt32AsyncWTime)(const char* ACompleteName, const s32 AValue, const s64 ATimeUs);
typedef s32 (__stdcall* TTSAppSetSystemVarUInt32AsyncWTime)(const char* ACompleteName, const u32 AValue, const s64 ATimeUs);
typedef s32 (__stdcall* TTSAppSetSystemVarInt64AsyncWTime)(const char* ACompleteName, const s64 AValue, const s64 ATimeUs);
typedef s32 (__stdcall* TTSAppSetSystemVarUInt64AsyncWTime)(const char* ACompleteName, const u64 AValue, const s64 ATimeUs);
typedef s32 (__stdcall* TTSAppSetSystemVarUInt8ArrayAsyncWTime)(const char* ACompleteName, const s32 ACount, const pu8 AValue, const s64 ATimeUs);
typedef s32 (__stdcall* TTSAppSetSystemVarInt32ArrayAsyncWTime)(const char* ACompleteName, const s32 ACount, const ps32 AValue, const s64 ATimeUs);
typedef s32 (__stdcall* TTSAppSetSystemVarInt64ArrayAsyncWTime)(const char* ACompleteName, const s32 ACount, const ps64 AValue, const s64 ATimeUs);
typedef s32 (__stdcall* TTSAppSetSystemVarDoubleArrayAsyncWTime)(const char* ACompleteName, const s32 ACount, const double* AValue, const s64 ATimeUs);
typedef s32 (__stdcall* TTSAppSetSystemVarStringAsyncWTime)(const char* ACompleteName, const char* AValue, const s64 ATimeUs);
typedef s32 (__stdcall* TTSAppSetSystemVarGenericAsyncWTime)(const char* ACompleteName, const char* AValue, const s64 ATimeUs);
typedef s32 (__stdcall* TDBGetSignalStartBitByPDUOffset)(const s32 ASignalStartBitInPDU, const s32 ASignalBitLength, const bool AIsSignalIntel, const bool AIsPDUIntel, const s32 APDUStartBit, const s32 APDUBitLength, ps32 AActualStartBit);
typedef s32 (__stdcall* TUIShowSaveFileDialog)(const char* ATitle, const char* AFileTypeDesc, const char* AFilter, const char* ASuggestFileName, char** ADestinationFileName);
typedef s32 (__stdcall* TUIShowOpenFileDialog)(const char* ATitle, const char* AFileTypeDesc, const char* AFilter, const char* ASuggestFileName, char** ADestinationFileName);
typedef s32 (__stdcall* TUIShowSelectDirectoryDialog)(char** ADestinationDirectory);
typedef s32 (__stdcall* TSetEthernetChannelCount)(const s32 ACount);
typedef s32 (__stdcall* TGetEthernetChannelCount)(ps32 ACount);
typedef s32 (__stdcall* TDBGetCANDBIndexById)(const s32 AId, ps32 AIndex);
typedef s32 (__stdcall* TDBGetLINDBIndexById)(const s32 AId, ps32 AIndex);
typedef s32 (__stdcall* TDBGetFlexRayDBIndexById)(const s32 AId, ps32 AIndex);
typedef s32 (__stdcall* TRegisterSystemVarChangeEvent)(const void* AObj, const char* ACompleteName, const TOnSysVarChange AEvent);
typedef s32 (__stdcall* TUnRegisterSystemVarChangeEvent)(const void* AObj, const char* ACompleteName, const TOnSysVarChange AEvent);
typedef s32 (__stdcall* TUnRegisterSystemVarChangeEvents)(const void* AObj, const TOnSysVarChange AEvent);
typedef s32 (__stdcall* TCallSystemAPI)(const char* AAPIName, const s32 AArgCount, const s32 AArgCapacity, char** AArgs);
typedef s32 (__stdcall* TCallLibraryAPI)(const char* AAPIName, const s32 AArgCount, const s32 AArgCapacity, char** AArgs);
typedef s32 (__stdcall* TIniReadStringWoQuotes)(const native_int AHandle, const char* ASection, const char* AKey, const char* AValue, ps32 AValueCapacity, const char* ADefault);
typedef s32 (__stdcall* TUIGraphicsAddSignal)(const char* AWindowCaption, const s32 AIdxSplit, const TSignalType ASgnType, const char* ASignalAddress);
typedef s32 (__stdcall* TUIGraphicsClearSignals)(const char* AWindowCaption, const s32 AIdxSplit);
typedef s32 (__stdcall* TGPGLoadExcel)(const char* AFileName, char** AGraphicProgramName, char** ASubModuleName);
typedef s32 (__stdcall* TRunProcedure)(const TCProcedure AProcedure);
typedef s32 (__stdcall* TOpenHelpDoc)(const char* AFileNameWoSuffix, const char* ATitle);
typedef s32 (__stdcall* TGetLangString)(const char* AEnglishStr, const char* AIniSection, char** ATranslatedStr);
typedef s32 (__stdcall* TConvertBlfToCsv)(const char* ABlfFile, const char* ACSVFile, const pbool AToTerminate);
typedef s32 (__stdcall* TConvertBlfToCsvWFilter)(const char* ABlfFile, const char* ACSVFile, const char* AFilterConf, const pbool AToTerminate);
typedef s32 (__stdcall* TStartLogWFileName)(const void* AObj, const char* AFileName);
typedef s32 (__stdcall* TConvertBlfToMatWFilter)(const char* ABlfFile, const char* AMatFile, const char* AFilterConf, const pbool AToTerminate);
typedef s32 (__stdcall* TConvertASCToMatWFilter)(const char* AASCFile, const char* AMatFile, const char* AFilterConf, const pbool AToTerminate);
typedef s32 (__stdcall* TConvertASCToCSVWFilter)(const char* AASCFile, const char* ACSVFile, const char* AFilterConf, const pbool AToTerminate);
typedef s32 (__stdcall* TSetDebugLogLevel)(const TLogLevel ALevel);
typedef s32 (__stdcall* TGetFormUniqueId)(const char* AClassName, const s32 AFormIdx, ps64 AUniqueId);
typedef s32 (__stdcall* Tpanel_clear_control)(const char* APanelName, const char* AControlName);
typedef s32 (__stdcall* Tset_form_unique_id)(const s64 AOldId, const s64 ANewId);
typedef s32 (__stdcall* Tshow_form)(const char* AFormCaption, const bool AShow);
typedef s32 (__stdcall* Tkill_form)(const char* AFormCaption);
typedef s32 (__stdcall* Tplace_form)(const char* AFormCaption, const s32 ALeft, const s32 ATop, const s32 AWidth, const s32 AHeight);
typedef s32 (__stdcall* Ttoggle_mdi_form)(const char* AFormCaption, const bool AIsMDI);
typedef s32 (__stdcall* Tget_language_id)(ps32 AId);
typedef s32 (__stdcall* Tcreate_form)(const char* AClassName, const bool AForceCreate, ps64 AFormId);
typedef s32 (__stdcall* Tset_form_caption)(const char* AOldCaption, const char* ANewCaption);
typedef s32 (__stdcall* Tenter_critical_section)(const void* AObj);
typedef s32 (__stdcall* Tleave_critical_section)(const void* AObj);
typedef s32 (__stdcall* Ttry_enter_critical_section)(const void* AObj);
typedef s32 (__stdcall* Tdb_load_can_db)(const char* ADBFileName, const char* ASupportedChannelsBased0, ps32 AId);
typedef s32 (__stdcall* Tdb_load_lin_db)(const char* ADBFileName, const char* ASupportedChannelsBased0, ps32 AId);
typedef s32 (__stdcall* Tdb_load_flexray_db)(const char* ADBFileName, const char* ASupportedChannelsBased0, ps32 AId);
typedef s32 (__stdcall* Tdb_unload_can_db)(const s32 AId);
typedef s32 (__stdcall* Tdb_unload_lin_db)(const s32 AId);
typedef s32 (__stdcall* Tdb_unload_flexray_db)(const s32 AId);
typedef s32 (__stdcall* Tdb_unload_can_dbs)(void);
typedef s32 (__stdcall* Tdb_unload_lin_dbs)(void);
typedef s32 (__stdcall* Tdb_unload_flexray_dbs)(void);
typedef s32 (__stdcall* TSecurityUpdateNewKeySync)(const s32 AChnIdx, const char* AOldKey, const u8 AOldKeyLength, const char* ANewKey, const u8 ANewKeyLength, const s32 ATimeoutMS);
typedef s32 (__stdcall* TSecurityUnlockWriteAuthoritySync)(const s32 AChnIdx, const char* AKey, const u8 AKeyLength, const s32 ATimeoutMS);
typedef s32 (__stdcall* TSecurityUnlockWriteAuthorityASync)(const s32 AChnIdx, const char* AKey, const u8 AKeyLength);
typedef s32 (__stdcall* TSecurityWriteStringSync)(const s32 AChnIdx, const s32 ASlotIndex, const char* AString, const u8 AStringLength, const s32 ATimeoutMs);
typedef s32 (__stdcall* TSecurityWriteStringASync)(const s32 AChnIdx, const s32 ASlotIndex, const char* AString, const u8 AStringLength);
typedef s32 (__stdcall* TSecurityReadStringSync)(const s32 AChnIdx, const s32 ASlotIndex, const char* AString, const pu8 AStringLength, const s32 ATimeoutMS);
typedef s32 (__stdcall* TSecurityUnlockEncChannelSync)(const s32 AChnIdx, const s32 ASlotIndex, const char* AString, const u8 AStringLength, const s32 ATimeoutMS);
typedef s32 (__stdcall* TSecurityUnlockEncChannelASync)(const s32 AChnIdx, const s32 ASlotIndex, const char* AString, const u8 AStringLength);
typedef s32 (__stdcall* TSecurityEncryptStringSync)(const s32 AChnIdx, const s32 ASlotIndex, const char* AString, const pu8 AStringLength, const s32 ATimeoutMS);
typedef s32 (__stdcall* TSecurityDecryptStringSync)(const s32 AChnIdx, const s32 ASlotIndex, const char* AString, const pu8 AStringLength, const s32 ATimeoutMS);
typedef s32 (__stdcall* Tset_channel_timestamp_deviation_factor)(const TLIBApplicationChannelType ABusType, const s32 AIdxLogicalChn, const s64 APCTimeUs, const s64 AHwTimeUs);
typedef s32 (__stdcall* Tstart_system_message_log)(const void* AObj, const char* ADirectory);
typedef s32 (__stdcall* Tend_system_message_log)(const void* AObj, char** ALogFileName);
typedef s32 (__stdcall* Tmask_fpu_exceptions)(const bool AMasked);
typedef s32 (__stdcall* Tcreate_process_shared_memory)(ppu8 AAddress, const s32 ASizeBytes);
typedef s32 (__stdcall* Tget_process_shared_memory)(ppu8 AAddress, ps32 ASizeBytes);
typedef s32 (__stdcall* Tclear_user_constants)(void);
typedef s32 (__stdcall* Tappend_user_constants_from_c_header)(const char* AHeaderFile);
typedef s32 (__stdcall* Tappend_user_constant)(const char* AConstantName, const double AValue, const char* ADesc);
typedef s32 (__stdcall* Tdelete_user_constant)(const char* AConstantName);
typedef s32 (__stdcall* Tget_mini_program_count)(ps32 ACount);
typedef s32 (__stdcall* Tget_mini_program_info_by_index)(const s32 AIndex, ps32 AKind, char** AProgramName, char** ADisplayName);
typedef s32 (__stdcall* Tcompile_mini_programs)(const char* AProgramNames);
typedef s32 (__stdcall* Tset_system_var_init_value)(const char* ACompleteName, const char* AValue);
typedef s32 (__stdcall* Tget_system_var_init_value)(const char* ACompleteName, char** AValue);
typedef s32 (__stdcall* Treset_system_var_to_init)(const char* ACompleteName);
typedef s32 (__stdcall* Treset_all_system_var_to_init)(const char* AOwner);
typedef s32 (__stdcall* Tget_system_var_generic_upg1)(const char* ACompleteName, char** AValue);
typedef s32 (__stdcall* Tmplib_load)(const char* AMPFileName,const bool ARunAfterLoad);
typedef s32 (__stdcall* Tmplib_unload)(const char* AMPFileName);
typedef s32 (__stdcall* Tmplib_unload_all)(void);
typedef s32 (__stdcall* Tmplib_run)(const char* AMPFileName);
typedef s32 (__stdcall* Tmplib_is_running)(const char* AMPFileName,bool* AIsRunning);
typedef s32 (__stdcall* Tmplib_stop)(const char* AMPFileName);
typedef s32 (__stdcall* Tmplib_run_all)(void);
typedef s32 (__stdcall* Tmplib_stop_all)(void);
typedef s32 (__stdcall* Tmplib_get_function_prototype)(const char* AGroupName,const char* AFuncName,const ppchar APrototype);
typedef s32 (__stdcall* Tmplib_get_mp_function_list)(const char* AGroupName,const ppchar AList);
typedef s32 (__stdcall* Tmplib_get_mp_list)(const ppchar AList);
typedef s32 (__stdcall* Tget_tsmaster_binary_location)(char** ADirectory);
typedef s32 (__stdcall* Tget_form_instance_count)(const char* AClassName, ps32 ACount);
typedef s32 (__stdcall* Tget_active_application_list)(char** ATSMasterAppNames);
typedef s32 (__stdcall* Tenumerate_hw_devices)(ps32 ACount);
typedef s32 (__stdcall* Tget_hw_info_by_index)(const s32 AIndex, PLIBHWInfo AHWInfo);
typedef s32 (__stdcall* Tui_graphics_set_measurement_cursor)(const char* AWindowCaption, const s64 ATimeUs);
typedef s32 (__stdcall* Tui_graphics_set_diff_cursor)(const char* AWindowCaption, const s64 ATime1Us, const s64 ATime2Us);
typedef s32 (__stdcall* Tui_graphics_hide_diff_cursor)(const char* AWindowCaption);
typedef s32 (__stdcall* Tui_graphics_hide_measurement_cursor)(const char* AWindowCaption);
typedef s32 (__stdcall* Tencode_string)(const char* ASrc, char** ADest);
typedef s32 (__stdcall* Tdecode_string)(const char* ASrc, char** ADest);
typedef s32 (__stdcall* Tis_realtime_mode)(pbool AValue);
typedef s32 (__stdcall* Tis_simulation_mode)(pbool AValue);
typedef s32 (__stdcall* Tui_ribbon_add_icon)(const char* AFormClassName, const char* ATabName, const char* AGroupName, const char* AButtonName, const s32 AIdxImageSmall, const s32 AIdxImageLarge);
typedef s32 (__stdcall* Tui_ribbon_del_icon)(const char* AFormClassName);
typedef s32 (__stdcall* Tpanel_create_control)(const char* APanelName, const char* AParentCtrlName, s32 AParentCtrlSubIdx, const char* AName, TLIBPanelControlType ACtrlType, float ALeft, float ATop, float AWidth, float AHeight, TLIBPanelSignalType AVarType, const char* AVarLink);
typedef s32 (__stdcall* Tpanel_delete_control)(const char* APanelName, const char* ACtrlName);
typedef s32 (__stdcall* Tpanel_set_var)(const char* APanelName, const char* ACtrlName, const TLIBPanelSignalType AVarType, const char* AVarLink);
typedef s32 (__stdcall* Tpanel_get_var)(const char* APanelName, const char* ACtrlName, PLIBPanelSignalType AVarType, char** AVarLink);
typedef s32 (__stdcall* Tpanel_get_control_count)(const char* APanelName, ps32 ACount);
typedef s32 (__stdcall* Tpanel_get_control_by_index)(const char* APanelName, const s32 AIndex, PLIBPanelControlType ACtrlType, char** AName);
typedef s32 (__stdcall* Tui_save_project)(const char* AProjectFullPath);
typedef s32 (__stdcall* Tretrieve_api_address)(const char* AApiName, ps32 AFlags, pnative_int AAddr);
typedef s32 (__stdcall* Tui_load_rpc_ip_configuration)(const char* AFileName);
typedef s32 (__stdcall* Tui_unload_rpc_ip_configuration)(const char* AFileName);
typedef s32 (__stdcall* Tui_unload_rpc_ip_configurations)(void);
typedef s32 (__stdcall* Tam_set_custom_columns)(const char* AModuleName, const char* AColumnsConfig);
typedef s32 (__stdcall* Twrite_realtime_comment_w_time)(const void* AObj, const char* AComment, const s64 ATimeUs);
typedef s32 (__stdcall* Tui_graphics_set_relative_time)(const char* AWindowCaption, const s64 ATimeUs);
typedef s32 (__stdcall* Tpanel_import_configuration)(const char* APanelName, const char* AFileName);
typedef s32 (__stdcall* Tui_graphics_set_y_axis_fixed_range)(const char* AWindowCaption, const s32 AIdxSplit, const char* ASignalName, const double AMin, const double AMax);
typedef s32 (__stdcall* Texport_system_messages)(const char* AFileName);
typedef s32 (__stdcall* Tui_graphics_export_csv)(const char* AWindowCaption, const char* ASgnNames, const char* AFileName, const s64 ATimeStartUs, const s64 ATimeEndUs);
typedef s32 (__stdcall* Tregister_usb_insertion_event)(const pvoid AObj, const TOnUSBPlugEvent AEvent);
typedef s32 (__stdcall* Tunregister_usb_insertion_event)(const pvoid AObj, const TOnUSBPlugEvent AEvent);
typedef s32 (__stdcall* Tregister_usb_removal_event)(const pvoid AObj, const TOnUSBPlugEvent AEvent);
typedef s32 (__stdcall* Tunregister_usb_removal_event)(const pvoid AObj, const TOnUSBPlugEvent AEvent);
typedef s32 (__stdcall* Tsecurity_check_custom_license_valid)(const char* ALicenseName);
typedef s32 (__stdcall* Tcall_model_initialization)(const pvoid AObj, const char* ADiagramName, const s32 AInCnt, const s32 AOutCnt, const PMBDDataType AInTypes, const PMBDDataType AOutTypes, pnative_int AHandle);
typedef s32 (__stdcall* Tcall_model_step)(const pvoid AObj, const native_int AHandle, const s64 ATimeUs, const pvoid AInValues, pvoid AOutValues);
typedef s32 (__stdcall* Tcall_model_finalization)(const pvoid AObj, const native_int AHandle);
typedef s32 (__stdcall* Tui_hide_main_form)(void);
typedef s32 (__stdcall* Tui_show_main_form)(const s32 ALeft, const s32 ATop, const s32 AWidth, const s32 AHeight);
typedef s32 (__stdcall* Tconfigure_can_regs)(const s32 AChn, const float ABaudrateKbps, const u32 ASEG1, const u32 ASEG2, const u32 APrescaler, const u32 ASJW, const bool AOnlyListen, const bool A120OhmConnected);
typedef s32 (__stdcall* Tconfigure_canfd_regs)(const s32 AChn, const float AArbBaudrateKbps, const u32 AArbSEG1, const u32 AArbSEG2, const u32 AArbPrescaler, const u32 AArbSJW, const float ADataBaudrateKbps, const u32 ADataSEG1, const u32 ADataSEG2, const u32 ADataPrescaler, const u32 ADataSJW, const TCANFDControllerType AControllerType, const TCANFDControllerMode AControllerMode, const bool A120OhmConnected);
typedef s32 (__stdcall* Tstart_log_verbose)(const pvoid AObj, s32 AFilesizeType, s64 ASizeValue);
typedef s32 (__stdcall* Tstart_log_w_filename_verbose)(const pvoid AObj, char* AFileName, s32 AFilesizeType, s64 ASizeValue);
typedef s32 (__stdcall* Ttsio_start_configuration)(void);
typedef s32 (__stdcall* Ttsio_end_configuration)(void);
typedef s32 (__stdcall* Ttsdi_config_sync)(const s32 AChn, const double ASampleRate, const s32 AInputThrsholdMv, const s32 AReportPWMFreq, const s32 ATimeoutMs);
typedef s32 (__stdcall* Ttsdo_config_sync)(const s32 AChn, const s32 AEnableReport, const double ASampleRate, const s32 AOutputLevel, const s32 AOutputModes, const s32 AOutputType, const s32 ATimeoutMs);
typedef s32 (__stdcall* Tset_di_channel_count)(const s32 ACount);
typedef s32 (__stdcall* Tset_do_channel_count)(const s32 ACount);
typedef s32 (__stdcall* Tset_ao_channel_count)(const s32 ACount);
typedef s32 (__stdcall* Tset_ai_channel_count)(const s32 ACount);
typedef s32 (__stdcall* Tget_ai_channel_count)(const ps32 ACount);
typedef s32 (__stdcall* Tget_ao_channel_count)(const ps32 ACount);
typedef s32 (__stdcall* Tget_do_channel_count)(const ps32 ACount);
typedef s32 (__stdcall* Tget_di_channel_count)(const ps32 ACount);
// >>> mp app prototype end <<<
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
