Nimfrodian/Overlord/src/BSW/GpioControl/ComCfg/ComModbus/ComModbus.cpp

#include "ComModbus.h"
#include "GpioControl.h"    // used for debug LED

typedef enum
{
    COM_MODBUS_TRANSMITTING = 0,
    COM_MODBUS_RECEIVING,
} ComModbus_transcieveStType;

static ComModbus_transcieveStType _mb2TrnscieveType = COM_MODBUS_TRANSMITTING;

void ComModbus_init(void)
{
    // set DE and RE pins for MAX485 module
    gpio_set_direction(DE_RE_PIN_MB0, GPIO_MODE_OUTPUT);
    gpio_set_direction(DE_RE_PIN_MB2, GPIO_MODE_OUTPUT);

    ComCfg_init();

    // Configure UART 2
    {
        uart_config_t uart2_config = {
                .baud_rate = COM_MODBUS_2_BAUDRATE,
                .data_bits = UART_DATA_8_BITS,
                .parity = UART_PARITY_DISABLE,
                .stop_bits = UART_STOP_BITS_1,
                .flow_ctrl = UART_HW_FLOWCTRL_DISABLE,
                .rx_flow_ctrl_thresh = 122,
                .source_clk = UART_SCLK_APB,
        };
        // Configure UART 2 pins
        uart_set_pin(UART_NUM_2, 17, 16, UART_PIN_NO_CHANGE, UART_PIN_NO_CHANGE);
        // Set UART 2 parameters
        uart_param_config(UART_NUM_2, &uart2_config);
        // Install UART 2 driver
        uart_driver_install(UART_NUM_2, 1024, 1024, 0, NULL, 0);

        // create transceive task
        xTaskCreatePinnedToCore(
        ComModbus_2_transceive,    // Function that should be called
        "ComModbus_2_transceive",   // Name of the task (for debugging)
        8192,            // Stack size (bytes)
        NULL,            // Parameter to pass
        1,               // Task priority
        NULL,            // Task handle
        1                // run on core 1
        );
    }

    // Configure UART 0
    {
        uart_config_t uart0_config = {
                .baud_rate = COM_MODBUS_0_BAUDRATE,
                .data_bits = UART_DATA_8_BITS,
                .parity = UART_PARITY_DISABLE,
                .stop_bits = UART_STOP_BITS_1,
                .flow_ctrl = UART_HW_FLOWCTRL_DISABLE,
                .rx_flow_ctrl_thresh = 122,
                .source_clk = UART_SCLK_APB,
        };
        // Configure UART 0 pins
        uart_set_pin(UART_NUM_0, UART_PIN_NO_CHANGE, UART_PIN_NO_CHANGE, UART_PIN_NO_CHANGE, UART_PIN_NO_CHANGE);
        // Set UART 0 parameters
        uart_param_config(UART_NUM_0, &uart0_config);
        // Install UART 0 driver
        uart_driver_install(UART_NUM_0, 1024, 1024, 0, NULL, 0);

        // create transceive task
        xTaskCreatePinnedToCore(
        ComModbus_0_transceive,    // Function that should be called
        "ComModbus_0_transceive",   // Name of the task (for debugging)
        8192,            // Stack size (bytes)
        NULL,            // Parameter to pass
        1,               // Task priority
        NULL,            // Task handle
        1                // run on core 1
        );
    }
}

void ComModbus_0_transceive(void* param)
{
    while (1)
    {
        // loop through all of the messages to check if any is ready to be sent
        for (uint16_t mbMsgIndx = 0; mbMsgIndx < NUM_OF_MODBUS_0_MSG; mbMsgIndx++)
        {
            // get message pointer
            ComCfg_Modbus0MsgDataType* txMsgPtr = ComCfg_get_mb0Config((ComCfg_modbus0MsgIndxType) mbMsgIndx);

            // check if message is ready to be sent
            if (1 == txMsgPtr->mbRdyForTx)
            {
                // Prepare for transmit
                gpio_set_level(DE_RE_PIN_MB0, 1);

                vTaskDelay(pdMS_TO_TICKS(1));

                // write the data to UART line
                uart_write_bytes(UART_NUM_0, (const char*) txMsgPtr->dataOut, txMsgPtr->dataOutCount);

                vTaskDelay(pdMS_TO_TICKS(1));

                // add 20ms for every 8 bytes of extra data to be sent
                TickType_t timeoutTime = pdMS_TO_TICKS(100 + 20 * txMsgPtr->dataOutCount / 8);
                uart_wait_tx_done(UART_NUM_0, timeoutTime);
                // prepare for receive
                gpio_set_level(DE_RE_PIN_MB0, 0);

                // erase anything that is stuck in UART 0 RX to prepare for response
                uart_flush_input(UART_NUM_0);

                // no need for response parse, simply flag as sent
                {
                    txMsgPtr->mbRdyForTx = 0;
                    txMsgPtr->mbRdyForParse = 0;
                }
                break;
            }
        }

        vTaskDelay(pdMS_TO_TICKS(COM_MODBUS_TASK_DELAY_TIME_MS));
    }


    // delete task if illegal state was reached
    vTaskDelete( NULL );
}

/**
 * @brief Function is used to copy the data from ModWriteBuffer into the premade Modbus buffer and flagging the message for TX (For Modbus 0)
 * @param MsgIndx Message index for the array of Modbus messages
 * @param ModWriteBuffer Pointer to data which is to be copied
 * @param DataTxSize Size of data to be sent
 * @param DataRxSize Size of data to be received as response
 * @return false if failed (message already prepared and not yet sent), true if successful
 */
bool ComModbus_0_writeMsg(uint16_t MsgIndx, uint8_t* ModWriteBuffer, uint8_t DataTxSize)
{
    bool success = 0;
    // get message pointer
    ComCfg_Modbus0MsgDataType* txMsgPtr = ComCfg_get_mb0Config((ComCfg_modbus0MsgIndxType) MsgIndx);

    // if message is not already waiting for TX then copy the data
    if (0 == txMsgPtr->mbRdyForTx)
    {
        // copy the data into the message pointer
        for (uint8_t i = 0; i < DataTxSize; i++)
        {
            txMsgPtr->dataOut[i] = ModWriteBuffer[i];
        }

        // add CRC
        unsigned int crc = CRC_16(txMsgPtr->dataOut, DataTxSize - 2);
        txMsgPtr->dataOut[DataTxSize - 2] = (crc >> 8) & 0xFF;  // CRC HI
        txMsgPtr->dataOut[DataTxSize - 1] = (crc >> 0) & 0xFF;  // CRC LOW

        // add send data size
        txMsgPtr->dataOutCount = DataTxSize;

        // flag message as ready for transmit
        txMsgPtr->mbRdyForTx = 1;

        // message was successfully copied
        success = 1;
    }
    return success;
}

void ComModbus_2_transceive(void* param)
{
    ComCfg_modbus2MsgIndxType sendingMsg = (ComCfg_modbus2MsgIndxType) 0;
    while (1)
    {
        if (COM_MODBUS_TRANSMITTING == _mb2TrnscieveType)
        {
            // loop through all of the messages to check if any is ready to be sent
            for (uint16_t mbMsgIndx = 0; mbMsgIndx < NUM_OF_MODBUS_2_MSG; mbMsgIndx++)
            {
                // get message pointer
                ComCfg_Modbus2MsgDataType* txMsgPtr = ComCfg_get_mb2Config((ComCfg_modbus2MsgIndxType) mbMsgIndx);

                // check if message is ready to be sent
                if (1 == txMsgPtr->mbRdyForTx)
                {
                    // Prepare for transmit
                    gpio_set_level(DE_RE_PIN_MB2, 1);

                    vTaskDelay(pdMS_TO_TICKS(1));

                    // write the data to UART line
                    uart_write_bytes(UART_NUM_2, (const char*) txMsgPtr->dataOut, txMsgPtr->dataOutCount);

                    vTaskDelay(pdMS_TO_TICKS(1));

                    // add 20ms for every 8 bytes of extra data to be sent
                    TickType_t timeoutTime = pdMS_TO_TICKS(100 + 20 * txMsgPtr->dataOutCount / 8);
                    uart_wait_tx_done(UART_NUM_2, timeoutTime);
                    // prepare for receive
                    gpio_set_level(DE_RE_PIN_MB2, 0);

                    // erase anything that is stuck in UART 2 RX to prepare for response
                    uart_flush_input(UART_NUM_2);

                    // note which message index is ready to be sent
                    sendingMsg = (ComCfg_modbus2MsgIndxType) mbMsgIndx;
                    // break out of the for loop and continue with receive
                    _mb2TrnscieveType = COM_MODBUS_RECEIVING;
                    break;
                }
            }
        }
        if (COM_MODBUS_RECEIVING == _mb2TrnscieveType)
        {
            static uint8_t timeoutCntr = 0;  // counter of how many times the message has timed out

            // get message pointer
            ComCfg_Modbus2MsgDataType* rxMsgPtr = ComCfg_get_mb2Config(sendingMsg);

            // read the data
            uint8_t length = uart_read_bytes(UART_NUM_2, rxMsgPtr->dataIn, rxMsgPtr->dataInCount, pdMS_TO_TICKS(100));

            // if the data count is correct then proceed with parsing
            if (rxMsgPtr->dataInCount == length)
            {
                // clear the request for transmit flag as it was processed, set the request for parse flag. Reset the timeout counter.
                rxMsgPtr->mbRdyForTx = 0;
                rxMsgPtr->mbRdyForParse = 1;
                timeoutCntr = 0;

                // clear any leftover data which is erroneous
                uart_flush_input(UART_NUM_2);
            }
            else
            {
                timeoutCntr++;
                uart_flush_input(UART_NUM_2);

                if (timeoutCntr > MODBUS_TIMEOUT_COUNTER_MAX_VAL)
                {
                    timeoutCntr = 0;
                    // clear the transmit flag - the sending was not successful
                    rxMsgPtr->mbRdyForTx = 0;
                }
            }
            // return transcieving type to transmit
            _mb2TrnscieveType = COM_MODBUS_TRANSMITTING;
        }

        vTaskDelay(pdMS_TO_TICKS(COM_MODBUS_TASK_DELAY_TIME_MS));
    }


    // delete task if illegal state was reached
    vTaskDelete( NULL );
}

/**
 * @brief Function is used to copy the data from ModWriteBuffer into the premade Modbus buffer and flagging the message for TX (For Modbus 2)
 * @param MsgIndx Message index for the array of Modbus messages
 * @param ModWriteBuffer Pointer to data which is to be copied
 * @param DataTxSize Size of data to be sent
 * @param DataRxSize Size of data to be received as response
 * @return false if failed (message already prepared and not yet sent), true if successful
 */
bool ComModbus_2_writeMsg(uint16_t MsgIndx, uint8_t* ModWriteBuffer, uint8_t DataTxSize, uint8_t DataRxSize)
{
    bool success = 0;
    // get message pointer
    ComCfg_Modbus2MsgDataType* txMsgPtr = ComCfg_get_mb2Config((ComCfg_modbus2MsgIndxType) MsgIndx);

    // if message is not already waiting for TX then copy the data
    if (0 == txMsgPtr->mbRdyForTx)
    {
        // copy the data into the message pointer
        for (uint8_t i = 0; i < DataTxSize; i++)
        {
            txMsgPtr->dataOut[i] = ModWriteBuffer[i];
        }

        // add CRC
        unsigned int crc = CRC_16(txMsgPtr->dataOut, DataTxSize - 2);
        txMsgPtr->dataOut[DataTxSize - 2] = (crc >> 8) & 0xFF;  // CRC HI
        txMsgPtr->dataOut[DataTxSize - 1] = (crc >> 0) & 0xFF;  // CRC LOW

        // add send and receive data size
        txMsgPtr->dataInCount = DataRxSize;
        txMsgPtr->dataOutCount = DataTxSize;

        // flag message as ready for transmit
        txMsgPtr->mbRdyForTx = 1;

        // message was successfully copied
        success = 1;
    }
    return success;
}
