Nimfrodian/Overlord/include/mdll.h

/*
*
* Module list file
*
*/
#pragma once

enum moduleList
{
    MODULE_INVALID = 0,
    MODULE_MAIN,

    MODULE_ERRH,
    MODULE_TIMH,
    MODULE_CANM,
    MODULE_PINA,
    MODULE_SERA,
    MODULE_TMRA,
    MODULE_RTDB,
    MODULE_DMAS,
    MODULE_DIOM,
    MODULE_MBCM,
    MODULE_NVSM,
    MODULE_DIMH,
};
