Nimfrodian/Overlord/include/mbcm.h

/*
*   Modbus control module
*   used to communicate with Modbus devices
*
*/

#pragma once

#include "rtdb.h"
#include "errh.h"
#include "driver/uart.h"

#define MBCM_API_INIT_U32                  ((uint32_t) 1)
#define MBCM_API_MB1_RUN_U32               ((uint32_t) 2)
#define MBCM_API_MB2_RUN_U32               ((uint32_t) 3)
#define MBCM_API_MB_PRERUN_U32             ((uint32_t) 4)

#define MBCM_ERR_WRONG_DATA_U32            ((uint32_t) 1)

#define MBCM_MAX_RELAY_BOARDS_U32          ((uint32_t) 16)   ///< max number of relay boards. Id's 1-16
#define MBCM_MAX_PWR_METERS_U32            ((uint32_t) 20)   ///< max number of power meters. Id's 1-20

#define MBCM_MB1_BAUDRATE_U32   ((uint32_t) 256000)   ///< baudrate for Modbus 1
#define MBCM_MB2_BAUDRATE_U32   ((uint32_t)   9600)   ///< baudrate for Modbus 2

#define MBCM_MB1_UART_NUM_STR       (UART_NUM_1)   ///< UART number for Modbus 1
#define MBCM_MB2_UART_NUM_STR       (UART_NUM_2)   ///< UART number for Modbus 1

typedef struct
{
} tMBCM_INITDATA_STR;

// Modbus available data
enum
{
    SDM120M_READ_VOLTAGE_V = 0,
    SDM120M_READ_CURRENT_A,
    SDM120M_ACTIVE_POWER_W,
    SDM120M_APPARENT_POWER_VA,
    SDM120M_REACTIVE_POWER_VAr,
    SDM120M_POWER_FACTOR,
    SDM120M_FREQUENCY,
    SDM120M_IMPORT_ACTIVE_ENERGY_kWh,
    SDM120M_EXPORT_ACTIVE_ENERGY_kWh,
    SDM120M_IMPORT_REACTIVE_ENERGY_kVArh,
    SDM120M_EXPORT_REACTIVE_ENERGY_kVArh,
    SDM120M_TOTAL_SYSTEM_POWER_DEMAND_W,
    SDM120M_MAXIMUM_TOTAL_SYSTEM_POWER_DEMAND_W,
    SDM120M_IMPORT_SYSTEM_POWER_DEMAND_W,
    SDM120M_MAXIMUM_IMPORT_SYSTEM_POWER_DEMAND_W,
    SDM120M_EXPORT_SYSTEM_POWER_DEMAND_W,
    SDM120M_MAXIMUM_EXPORT_SYSTEM_POWER_DEMAND,
    SDM120M_CURRENT_DEMAND_A,
    SDM120M_MAXIMUM_CURRENT_DEMAND_A,
    SDM120M_TOTAL_ACTIVE_ENERGY_kWh,
    SDM120M_TOTAL_REACTIVE_ENERGY_kVArh,
    SDM120M_NUM_OF_READ,
};

const uint16_t mbcm_sdm120mStartAddrs_aU16[SDM120M_NUM_OF_READ] =
{
    [SDM120M_READ_VOLTAGE_V] = 0x0000,
    [SDM120M_READ_CURRENT_A] = 0x0006,
    [SDM120M_ACTIVE_POWER_W] = 0x000C,
    [SDM120M_APPARENT_POWER_VA] = 0x0012,
    [SDM120M_REACTIVE_POWER_VAr] = 0x0018,
    [SDM120M_POWER_FACTOR] = 0x001E,
    [SDM120M_FREQUENCY] = 0x0046,
    [SDM120M_IMPORT_ACTIVE_ENERGY_kWh] = 0x0048,
    [SDM120M_EXPORT_ACTIVE_ENERGY_kWh] = 0x004A,
    [SDM120M_IMPORT_REACTIVE_ENERGY_kVArh] = 0x004C,
    [SDM120M_EXPORT_REACTIVE_ENERGY_kVArh] = 0x004E,
    [SDM120M_TOTAL_SYSTEM_POWER_DEMAND_W] =0x0054,
    [SDM120M_MAXIMUM_TOTAL_SYSTEM_POWER_DEMAND_W] = 0x0056,
    [SDM120M_IMPORT_SYSTEM_POWER_DEMAND_W] = 0x0058,
    [SDM120M_MAXIMUM_IMPORT_SYSTEM_POWER_DEMAND_W] = 0x005A,
    [SDM120M_EXPORT_SYSTEM_POWER_DEMAND_W] = 0x005C,
    [SDM120M_MAXIMUM_EXPORT_SYSTEM_POWER_DEMAND] = 0x005E,
    [SDM120M_CURRENT_DEMAND_A] = 0x0102,
    [SDM120M_MAXIMUM_CURRENT_DEMAND_A] = 0x0108,
    [SDM120M_TOTAL_ACTIVE_ENERGY_kWh] = 0x0156,
    [SDM120M_TOTAL_REACTIVE_ENERGY_kVArh] = 0x0158,
};

void mbcm_init(tMBCM_INITDATA_STR* DiomCfg);
