Nimfrodian/Overlord/other/tsmasterWorkspace/Simulation/RBSCAN.ini

[RBSCAN]
Init=0
AutoSend=1
NetworkCnt=1
AutoStart=0
FEnableAutomaticAlgorithm=1
PreventExternalAutoStart=0
NotCheckRxMessageForHIL=1
N0=CH0_CAN_database

[CH0_CAN_database]
Name=CAN_database
Chn=0
Active=0
NodeCount=3
N0=CH0_CAN_database_RoomController
N1=CH0_CAN_database_HomeAssistantESP
N2=CH0_CAN_database_TS_SimulationNode

[CH0_CAN_database_RoomController]
Name=RoomController
Active=0
MsgCount=20
M0=CH0_CAN_database_RoomController_RC_SDM120M_1_0
M1=CH0_CAN_database_RoomController_RC_SDM120M_2_0
M2=CH0_CAN_database_RoomController_RC_SDM120M_3_0
M3=CH0_CAN_database_RoomController_RC_SDM120M_4_0
M4=CH0_CAN_database_RoomController_RC_SDM120M_5_0
M5=CH0_CAN_database_RoomController_RC_SDM120M_6_0
M6=CH0_CAN_database_RoomController_RC_SDM120M_7_0
M7=CH0_CAN_database_RoomController_RC_SDM120M_8_0
M8=CH0_CAN_database_RoomController_RC_SDM120M_9_0
M9=CH0_CAN_database_RoomController_RC_SDM120M_10_0
M10=CH0_CAN_database_RoomController_RC_SDM120M_11_0
M11=CH0_CAN_database_RoomController_RC_SDM120M_12_0
M12=CH0_CAN_database_RoomController_RC_SDM120M_13_0
M13=CH0_CAN_database_RoomController_RC_SDM120M_14_0
M14=CH0_CAN_database_RoomController_RC_SDM120M_15_0
M15=CH0_CAN_database_RoomController_RC_SDM120M_16_0
M16=CH0_CAN_database_RoomController_RC_SDM120M_17_0
M17=CH0_CAN_database_RoomController_RC_SDM120M_18_0
M18=CH0_CAN_database_RoomController_RC_SDM120M_19_0
M19=CH0_CAN_database_RoomController_RC_SDM120M_20_0

[CH0_CAN_database_RoomController_RC_SDM120M_1_0]
Name=RC_SDM120M_1_0
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
RCCount=0
CRCCount=0
ExprCount=0
PDUManualConfigCnt=0

[CH0_CAN_database_RoomController_RC_SDM120M_18_0]
Name=RC_SDM120M_18_0
Active=0
IsTx=1
MsgType=0
Cycle=0
FFastCycle=0
FFastMsgRepetition=0
StartDelay=0
MsgDelay=0
Init=0,0,0,0,0,0,0,0
RCCount=0
CRCCount=0
ExprCount=0
PDUManualConfigCnt=0

[CH0_CAN_database_RoomController_RC_SDM120M_19_0]
Name=RC_SDM120M_19_0
Active=0
IsTx=1
MsgType=0
Cycle=0
FFastCycle=0
FFastMsgRepetition=0
StartDelay=0
MsgDelay=0
Init=0,0,0,0,0,0,0,0
RCCount=0
CRCCount=0
ExprCount=0
PDUManualConfigCnt=0

[CH0_CAN_database_RoomController_RC_SDM120M_20_0]
Name=RC_SDM120M_20_0
Active=0
IsTx=1
MsgType=0
Cycle=0
FFastCycle=0
FFastMsgRepetition=0
StartDelay=0
MsgDelay=0
Init=0,0,0,0,0,0,0,0
RCCount=0
CRCCount=0
ExprCount=0
PDUManualConfigCnt=0

[CH0_CAN_database_HomeAssistantESP]
Name=HomeAssistantESP
Active=0
MsgCount=0

[CH0_CAN_database_TS_SimulationNode]
Name=TS_SimulationNode
Active=0
MsgCount=243
M0=CH0_CAN_database_TS_SimulationNode_Lux_Measurement
M1=CH0_CAN_database_TS_SimulationNode_RelayFeedback_64_127
M2=CH0_CAN_database_TS_SimulationNode_DMAS_cmd_msg_tE
M3=CH0_CAN_database_TS_SimulationNode_DMAS_cmd_msg_tB
M4=CH0_CAN_database_TS_SimulationNode_DMAS_cmd_msg_tF32
M5=CH0_CAN_database_TS_SimulationNode_DMAS_cmd_msg_tS32
M6=CH0_CAN_database_TS_SimulationNode_DMAS_cmd_msg_tS16
M7=CH0_CAN_database_TS_SimulationNode_DMAS_cmd_msg_tS8
M8=CH0_CAN_database_TS_SimulationNode_DMAS_cmd_msg_tU32
M9=CH0_CAN_database_TS_SimulationNode_DMAS_cmd_msg_tU16
M10=CH0_CAN_database_TS_SimulationNode_DMAS_res_msg
M11=CH0_CAN_database_TS_SimulationNode_DMAS_cmd_msg_tU8
M12=CH0_CAN_database_TS_SimulationNode_Dimmer_errh_msg3
M13=CH0_CAN_database_TS_SimulationNode_Dimmer_errh_msg2
M14=CH0_CAN_database_TS_SimulationNode_Dimmer_errh_msg1
M15=CH0_CAN_database_TS_SimulationNode_Dimmer_errh_msg0
M16=CH0_CAN_database_TS_SimulationNode_DimmerResponseMsg2
M17=CH0_CAN_database_TS_SimulationNode_DimmerResponseMsg1
M18=CH0_CAN_database_TS_SimulationNode_DimmerControlMsg
M19=CH0_CAN_database_TS_SimulationNode_RelayInvrtReq
M20=CH0_CAN_database_TS_SimulationNode_RelayDisbleReq
M21=CH0_CAN_database_TS_SimulationNode_GpioSts
M22=CH0_CAN_database_TS_SimulationNode_RelayFeedback_0_63
M23=CH0_CAN_database_TS_SimulationNode_RC_SDM120M_1_10
M24=CH0_CAN_database_TS_SimulationNode_RC_SDM120M_1_9
M25=CH0_CAN_database_TS_SimulationNode_RC_SDM120M_1_8
M26=CH0_CAN_database_TS_SimulationNode_RC_SDM120M_1_7
M27=CH0_CAN_database_TS_SimulationNode_RC_SDM120M_1_6
M28=CH0_CAN_database_TS_SimulationNode_RC_SDM120M_1_5
M29=CH0_CAN_database_TS_SimulationNode_RC_SDM120M_1_4
M30=CH0_CAN_database_TS_SimulationNode_RC_SDM120M_1_3
M31=CH0_CAN_database_TS_SimulationNode_RC_SDM120M_1_2
M32=CH0_CAN_database_TS_SimulationNode_RC_SDM120M_1_1
M33=CH0_CAN_database_TS_SimulationNode_RC_SDM120M_2_10
M34=CH0_CAN_database_TS_SimulationNode_RC_SDM120M_2_9
M35=CH0_CAN_database_TS_SimulationNode_RC_SDM120M_2_8
M36=CH0_CAN_database_TS_SimulationNode_RC_SDM120M_2_7
M37=CH0_CAN_database_TS_SimulationNode_RC_SDM120M_2_6
M38=CH0_CAN_database_TS_SimulationNode_RC_SDM120M_2_5
M39=CH0_CAN_database_TS_SimulationNode_RC_SDM120M_2_4
M40=CH0_CAN_database_TS_SimulationNode_RC_SDM120M_2_3
M41=CH0_CAN_database_TS_SimulationNode_RC_SDM120M_2_2
M42=CH0_CAN_database_TS_SimulationNode_RC_SDM120M_2_1
M43=CH0_CAN_database_TS_SimulationNode_RC_SDM120M_3_10
M44=CH0_CAN_database_TS_SimulationNode_RC_SDM120M_3_9
M45=CH0_CAN_database_TS_SimulationNode_RC_SDM120M_3_8
M46=CH0_CAN_database_TS_SimulationNode_RC_SDM120M_3_7
M47=CH0_CAN_database_TS_SimulationNode_RC_SDM120M_3_6
M48=CH0_CAN_database_TS_SimulationNode_RC_SDM120M_3_5
M49=CH0_CAN_database_TS_SimulationNode_RC_SDM120M_3_4
M50=CH0_CAN_database_TS_SimulationNode_RC_SDM120M_3_3
M51=CH0_CAN_database_TS_SimulationNode_RC_SDM120M_3_2
M52=CH0_CAN_database_TS_SimulationNode_RC_SDM120M_3_1
M53=CH0_CAN_database_TS_SimulationNode_RC_SDM120M_4_10
M54=CH0_CAN_database_TS_SimulationNode_RC_SDM120M_4_9
M55=CH0_CAN_database_TS_SimulationNode_RC_SDM120M_4_8
M56=CH0_CAN_database_TS_SimulationNode_RC_SDM120M_4_7
M57=CH0_CAN_database_TS_SimulationNode_RC_SDM120M_4_6
M58=CH0_CAN_database_TS_SimulationNode_RC_SDM120M_4_5
M59=CH0_CAN_database_TS_SimulationNode_RC_SDM120M_4_4
M60=CH0_CAN_database_TS_SimulationNode_RC_SDM120M_4_3
M61=CH0_CAN_database_TS_SimulationNode_RC_SDM120M_4_2
M62=CH0_CAN_database_TS_SimulationNode_RC_SDM120M_4_1
M63=CH0_CAN_database_TS_SimulationNode_RC_SDM120M_5_10
M64=CH0_CAN_database_TS_SimulationNode_RC_SDM120M_5_9
M65=CH0_CAN_database_TS_SimulationNode_RC_SDM120M_5_8
M66=CH0_CAN_database_TS_SimulationNode_RC_SDM120M_5_7
M67=CH0_CAN_database_TS_SimulationNode_RC_SDM120M_5_6
M68=CH0_CAN_database_TS_SimulationNode_RC_SDM120M_5_5
M69=CH0_CAN_database_TS_SimulationNode_RC_SDM120M_5_4
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
RCCount=0
CRCCount=0
ExprCount=0
PDUManualConfigCnt=0

[CH0_CAN_database_TS_SimulationNode_RC_SDM120M_20_0]
Name=RC_SDM120M_20_0
Active=0
IsTx=0
MsgType=0
Cycle=0
FFastCycle=0
FFastMsgRepetition=0
StartDelay=0
MsgDelay=0
Init=0,0,0,0,0,0,0,0
RCCount=0
CRCCount=0
ExprCount=0
PDUManualConfigCnt=0
