Nimfrodian/Overlord/other/tsmasterWorkspace/UI.ini

[CANFDTraceOptions]
UICommon=0,-1,0,0,Q0FOIC8gQ0FOIEZEIFRyYWNl,100,345,2147091579955552873,0
UIFilter=
UIConf=2276,-1,0,0,0,0,1,REVGQVVMVA__,C:\Users\Nimfrodian\AppData\Local\Programs\TOSUN\TSMaster\Configuration\TOSUN\TSMaster\Logging\Snapshot\,Snapshot
IdRemember0=521,502,513,
FilterStr=
FilterIsPass=1
FilterEnabled=0
HWidth=146,120,73,59,112,50,150,80,40,40,90,40,40,1800,112,150,50,60,55,200,200
HVis=-1,0,-1,-1,-1,-1,-1,-1,-1,-1,0,0,0,-1,0,0,0,0,0,0,0

[CANFDTransmit]
BypassPreTx=0
MessageCnt=1
M0=3;Q0FOX2RhdGFiYXNl;RGltbWVyQ29udHJvbE1zZw__;149;0;0;8;0;0,0,0,232,3,4,0,0,0,0,0,0,0,0,0,0,0,0,0,0,0,0,0,0,0,0,0,0,0,0,0,0,0,0,0,0,0,0,0,0,0,0,0,0,0,0,0,0,0,0,0,0,0,0,0,0,0,0,0,0,0,0,0,0,;;0;0;0;0;0;0;0;0
M0S0=VHJpZ2dlcmluZ1RpbWVfMTBtcw__;0;24;1;0;0;16777215;1;0;0;MTBtcw__;;6;0;0;0;0;0;838860;0;838860.75
M0S1=RW5kRHV0eUN5Y2xl;0;10;1;24;0;1000;1;0;0;MC4xJQ__;;6;0;0;0;0;1000;51;1000;50
M0S2=VHJpZ2dlcmluZ0luZGV4;0;24;1;40;0;16777215;1;0;0;;;6;0;0;0;0;4;838860;4;838860.75
M0AutoSARPDU=0
M0PDUNum=0
SgnPnlPercent=0.5
Protocol=1
MsgVis=-1,-1,-1,-1,-1,-1,-1,-1,-1,0,0,0,0,0,0,-1,-1,-1,-1,-1,-1,-1,-1,-1
MsgPos=0,1,2,3,4,5,6,7,8,9,10,11,12,13,14,15,16,17,18,19,20,21,22,23
SgnVis=-1,-1,-1,-1,-1,-1,-1,0,0,0,-1
SgnPos=0,1,2,3,4,5,6,7,8,9,10
UICommon=0,-1,0,0,Q0FOIC8gQ0FOIEZEIFRyYW5zbWl0,100,323,1654510370752173194,0
UIFilter=

[Graphics]
SgnCNT=4
gph=4294967295,4278190080,4278190080,1,0,0,562.048736961287,20,100000,0,0,-1,DEFAULT,20,0,0,0,-1
ui0=-1;0;0;4294901760;MCxBY3RpdmVQd3JfVyxSQ19TRE0xMjBNXzFfMSwwLDUwMiwwLDIsMjI0LjYwMDAwNjEwMzUxNiwzMDAuNSwxLDAsMCwtMSwzMiwwLFcsLDAsMCwwLDEsLTEsMjI2LDIyNywwLDEwMCwxLCwwLCws;"";1;0;0
ui1=-1;0;0;4278222592;MCxUb3RhbEFjdHZFbmVyZ3lfa1doLFJDX1NETTEyME1fMV85LDAsNTEwLDAsMiwxMi40MzIwMDAxNjAyMTczLDEyLjc2OTAwMDA1MzQwNTgsMSwwLDMyLC0xLDMyLDAsa1doLCwwLDAsMCwxLC0xLDEyLjQ0LDEyLjU1LDAsMTAwLDEsLDAsLCw_;"";1;0;0
ui2=-1;0;0;4278190335;MCxBY3RpdmVQd3JfVyxSQ19TRE0xMjBNXzJfMSwwLDUxMywwLDIsMCwxLDEsMCwwLC0xLDMyLDAsVywsMCwwLDAsMSwtMSwwLDEsMCwxMDAsMSwsMCwsLA__;"";1;0;0
ui3=-1;0;0;4286545664;MCxUb3RhbEFjdHZFbmVyZ3lfa1doLFJDX1NETTEyME1fMl85LDAsNTIxLDAsMiwwLDEsMSwwLDMyLC0xLDMyLDAsa1doLCwwLDAsMCwxLC0xLDAsMSwwLDEwMCwxLCwwLCws;"";1;0;0
HName=Group 1
UIVis=-1,-1,-1,-1,-1,-1,0,0,0,0,0,0
UIWidth=80,194,194,21,64,64,64,64,64,64
GridHeight=1090
YMax=0
SplitCount=1
TotalHeight=1092
PersistentSel=1
DisplayFrameDotSgn=0
ShowSelFloatingCur=0
Heights=1;0;
UICommon=0,-1,0,0,R3JhcGhpY3M_,100,335,4588042578109172931,0
UIFilter=
UISettings=0,2,-1,362
